naokiiwakami/analog2.0/02_panel/02_panel_doc_v1_0.pdf

## Analog 2.0 ドキュメンテーション

### Vol. 2

# パネルの製作

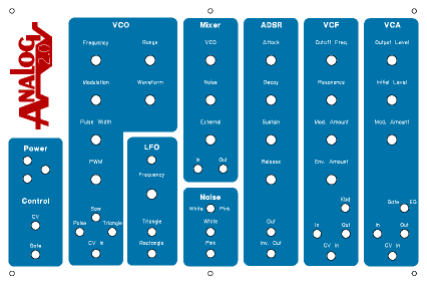
[picture p7: figure]

バージョン: 1.0
作成日：2008 年 1 月 25 日

Analog2.0 ドキュメンテーション
Vol.2 パネルの製作
Copyright (C) Naoki Iwakami. All rights reserved. | 2

目次

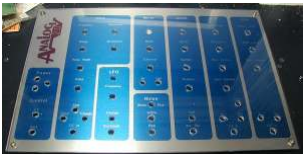
[picture p8: figure]

Copyright (C) Naoki Iwakami. All rights reserved. | 3
1. このドキュメントの目的

このドキュメントは、Analog2.0 のパネルの制作例を解説するものです。 Analog2.0 試作機におけるパネルの設計例をもとに、実際にパネルを製作する方法を解説 します。

パネルは、製作者の皆さんの工夫でどのように製作しても良く、このドキュメントで紹介 する制作方法は一例としてとらえてください。また、筐体の製作は Analog2.0 では紹介し ません。かわりに、試作機の実装例を写真で紹介します。最低限の手抜き製作の例です。

2. 製作例の紹介
2.1. パネル設計例の概要
ここで紹介するパネル設計例は、試作機で用いたものです。(図 2-1)

設計例では、図 2-2 のように、300mm x 200mm x 1mm のアルミ板と透明アクリル板で OHP シートを挟み込み構成します。OHP シートには、パネルのアートワークを印刷しま す。部品の取り付け穴は、重ねた状態でドリルを貫通させます。簡易的な設計ですが、以 下のメリットがあります

- パネル製作で一番面倒な塗装とレタリングを省くことができる
- ドリルで穴をあける際、OHP シートに目印をつけておけば、けがきをする必要がない

図 2-1 試作したパネル

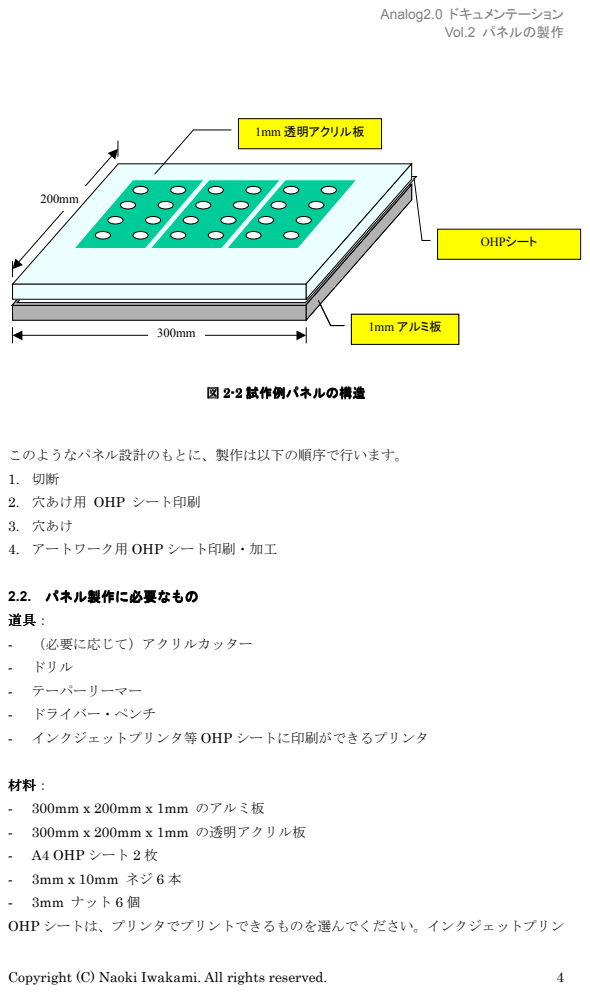
[picture p9: page 4]
Copyright (C) Naoki Iwakami. All rights reserved.; 図 2-2 試作例パネルの構造; 1mm アルミ板; OHPシート; 1mm 透明アクリル板

このようなパネル設計のもとに、製作は以下の順序で行います。
2. 穴あけ用 OHP シート印刷
3. 穴あけ
4. アートワーク用 OHP シート印刷・加工

2.2. パネル製作に必要なもの
- （必要に応じて）アクリルカッター
- ドリル
- テーパーリーマー
- ドライバー・ペンチ
- インクジェットプリンタ等 OHP シートに印刷ができるプリンタ

- 300mm x 200mm x 1mm のアルミ板
- 300mm x 200mm x 1mm の透明アクリル板
- A4 OHP シート 2 枚
- 3mm ナット 6 個
OHP シートは、プリンタでプリントできるものを選んでください。インクジェットプリン

Copyright (C) Naoki Iwakami. All rights reserved. | 5

タ・レーザープリンタ等、各プリンタタイプ用の OHP シートが販売されています。

ネジとナットは、重ね合わせたアルミ板・アクリル板・OHP シートを固定するために使い ます。

2.3. 材料の切断
パネルの製作にあたって、まずは始めに、材料のアルミ板とアクリルを希望の大きさに切 断します。最も推奨する方法は、初めから希望の大きさに切られている板を入手してしま うことです。道具を用意する必要がないし簡単で確実です。希望の大きさのものがない場 合にはホームセンターに依頼して切ってもらうと いう方法もあります。この試作機では アルミ板は 300mm x 200mm x 1mm のできあいのものを使い、アクリル板は自前で切断 しました。アクリル板の切断にはアクリルカッターを使います。

アルミ版を切断するには、金鋸を使う方法がすぐに思いつきますが、厚さ 1mm 程度のアル ミ板ならカッターナイフで切断できるようです。リンクが生きている限り以下のサイトが 参考になります。
http://webryalbum.biglobe.ne.jp/myalbum/1003289007923048b35a00dd242ffab118c63f430/65490414752138311

なお、A4 OHP シートのサイズは、297mm x 210mm で、300x200 と多少違っています。 はみ出る部分を切断する必要があります。これは仕上げ段階で行うと作業がしやすいです。

2.4. 穴あけ用 OHP シート印刷
次にパネルの穴あけを行います。試作例では、製作を簡単にするため、以下の手順で穴あ けを行います。

### 1. 穴あけ位置がマークしてあるアートワークを OHP シートに印刷する

### 2. 印刷した OHP シートを、アルミ板とアクリル板の間に挟みこむ

### 3. アートワークのマークに従い穴あけを行う

この節では、穴あけ用の OHP シートを印刷します。このドキュメントと同封してある panel_with_reference.pdf を印刷してください。以下は印刷時の注意事項です。

- プリント時の用紙選択にて、OHP シートを選びます。
- 高画質を選んでください。（色が濃いほうが作業しやすいため）
- 縮尺は 100%で印刷してください。

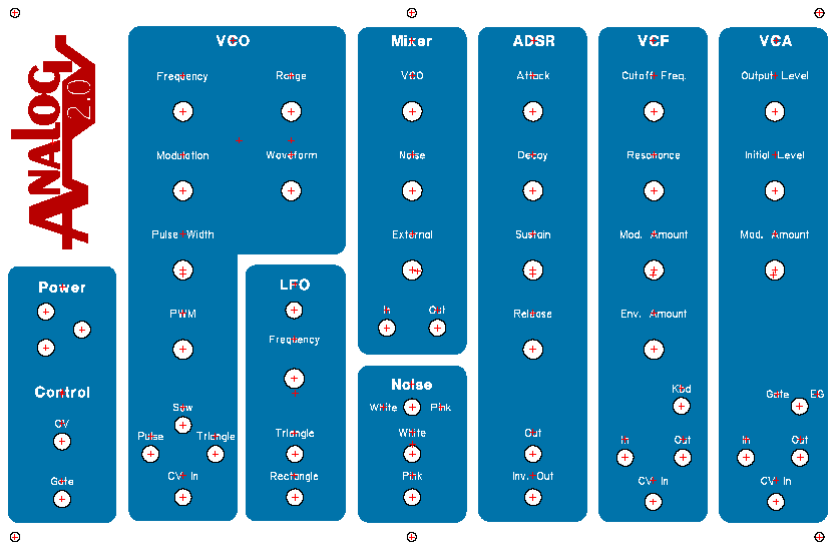
[picture p10: figure]

Copyright (C) Naoki Iwakami. All rights reserved. | 6
- 印刷後、すぐに印刷面に触らないようにしてください。OHP シートへの印刷は、イン クが乾きにくいことがよくあります。
- 印刷後、正しい縮尺で印刷されたかどうかの確認を必ず行ってください。方法はあとで 詳しく解説します。

参考までに、Adobe Reader 8 から印刷する際の、オプション設定は以下のとおりです。下 線が引いてあるところは、デフォルトから変更する必要のあるところです。

印刷範囲 | すべて
ページ部数 | 1
ページの拡大/縮小 | なし
自動回転と中央配置 | あり
ページサイズに合わせて用紙を選択 | なし

印刷を実行すると、図 2-3 のようなレイアウトが印刷されます。このレイアウトには、ドリ ル位置にセンターマーク（赤いプラス印）が打ってあるので、最終的なパネルシートとし ては使えません。ですが、パネルに挟み込むことで穴あけの際の位置決めに使います。こ のようにするとパネルへのけがきが不要になり、穴あけ作業が簡単になります。

図 2-3 ドリルガイド用 ドリルガイド用 OHP シート

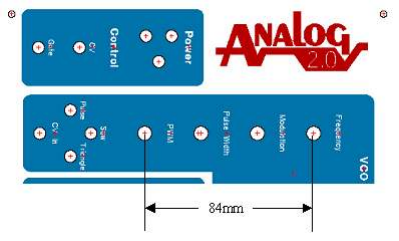
[picture p11: figure]

Copyright (C) Naoki Iwakami. All rights reserved. | 7

さて、OHP シートがプリントされたら、正しい縮尺で印刷されたかどうかチェックします。 印刷されたシートの、VCO 枠内 Frequency と PWM それぞれのセンターマークの距離 を測ります。84mm になっていれば OK です（図 2-4）。違っていたら、どこかに設定違い がないか確認してプリントしなおしてください。

図 2-4 OHP シート OHP シート縮尺確認

2.5. 穴あけ
OHP シートを印刷したら、いよいよ穴あけの開始です。 穴あけは、次のような手順で行います。

### 1. OHP シートをアルミ板とアクリル板で挟み込む

### 2. 四隅のネジ穴に穴をあけ、ネジで固定する

### 3. パネル部品用の穴をあける

OHP シートの固定
穴あけの最初の作業は、OHP シートをアルミ板とアクリル板で挟み込むことです。シート を正しい位置に配置して、しっかりと挟み込みます。位置あわせは、四隅のネジ穴位置が、 各々の角から等距離になるように行うとやりやすいと思います。ここで決まる配置が仕上 がりの配置になりますから注意深く作業してください。
アクリル板の防護シートは透明なら貼ったままにしておいてください。アルミ板の防護シ ートもまだ貼ったままにしておいてください。

OHP シートを固定する際、シートの両面の何箇所かに両面テープを貼っておくと作業が進 めやすいかもしれません。決めた位置からのずれを防止できるからです。

Copyright (C) Naoki Iwakami. All rights reserved. | 8

ネジ穴のドリル
OHP シートを固定したら穴あけ作業に入ります。まずは、隅のネジ穴からあけてゆきます。 ネジ穴は 3.2mm のドリルであけてください。
先にネジ穴をあけて、アクリル板・OHP シート・アルミ板を固定してしまうと、その後 はお互いがずれなくなるため、その後の作業が行いやすくなります。逆に、この作業で３ 枚がずれてしまうと、挽回するのは大変ですから、慎重に作業してください。

ネジ穴作業は、以下のような流れで行います。

### 1. まず、四隅のうちどれか一つに穴あけする。

### 2. あけた穴にネジを通してナットで締め固定してしまう。

### 3. 今あけた穴の対角に穴あけをし、ネジで固定する。

### 4. 残り二つの角の穴をあけ、ネジで固定する。

### 5. パネル上側と下側に残る二つのネジ穴をあける。ネジでの固定は必須ではない。

一つ一つのネジ穴は、以下の手順であけます。

### 1. アルミ版、OHP シート、アクリル板は重ねたまま穴あけする。

### 2. あける穴のセンターマーク位置にポンチで印をつける。なるべく垂直に見て印をつける

ようにしてポンチがセンターマークからずれないように気をつける。
3. 3.2mm ドリルを使って穴あけする。

パネル穴のドリル
ネジ穴をあけて、四隅をネジで固定したら、いよいよパネル部品の穴をあけてゆきます。 あけるべき穴のミリ数は、添付のシート panel_with_drill_sizes.pdf に記入してあります。 今度はドリル径が大きいので、位置ずれを起こさないように注意して作業してください。 下記は筆者がとったドリル方法です。比較的安い道具で失敗の少ない穴あけができます。

### 1. あける穴のセンターマークにあわせてポンチを打つ

2. 1.5mm 程度のドリルを使い、まずは小さな穴をあける。この作業はハンドドリルを使 ったほうがずれを起こしにくい。このドリルは細いほど良い。
3. 5mm 程度のドリルを使い、大きな穴をあける。

### 4. テーパーリーマーを使って穴を必要な大きさまで広げる。

ここまでできたら穴あけ作業は完了です。

Copyright (C) Naoki Iwakami. All rights reserved. | 9
2.6. アートワーク用 OHP シートの印刷・加工 穴あけが完了したら、仕上げの作業に入ります。
ここまで穴あけガイドに使っていた OHP シートは、作業を通して損傷しています。この シートは破棄して、アートワーク用に別の OHP シートを印刷して仕上げにはそちらを使 います。

アートワーク用の pdf ファイル panel.pdf を印刷してください。印刷の要領はドリル用の ものと同じです。縮尺の確認方法も同じですが、今回はセンタードリルがないので、ドリ ル穴のふちなどを使ってドリル穴間隔の計測をしてください。

次に、ネジで固定してあるアクリル板、アルミ板をいったんはずして、新しい OHP シー トを挟み込みます。その際、ドリル穴部分のシートが邪魔になるので、以下の方法いずれ かで取り除きます。

### 1. 革製品用のポンチを使って穴を打ち抜く

### 2. OHP シートをアクリルとアルミで挟みこんでネジで固定した後、ドリル穴部分のシー

トをカッターナイフでくりぬく

筆者は 1 の方法を使いました。きれいに打ち抜くには若干練習が必要ですが、慣れると能 率よく作業できます。

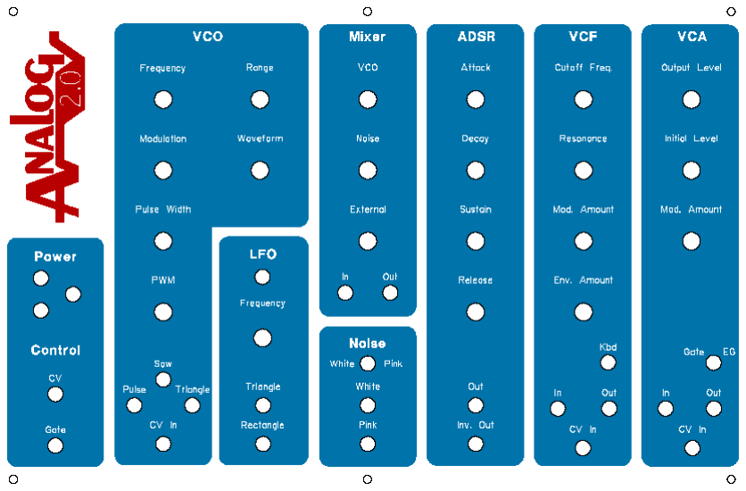
[picture p12: figure]

Copyright (C) Naoki Iwakami. All rights reserved. | 10

図 2-5 アートワーク用 OHP シートのレイアウト

さて、これでパネルは出来上がりました。大体図 2-1 のようになりましたか？

3. 筐体について

Analog2.0 で紹介するパネルの製作例は以上です。しかし、このままではシンセサイザー モジュールの製作はままならないはずです。パネルを立ててもすぐ倒れてしまうからです。

製作を進めるには、パネルを何かのケースに固定する必要があります。もっとも良いのは 筐体に収めてしまうことです。筐体を設計する際には、内側の奥行きが最低でも 100mm 必 要です。できれば 120mm 程度はあったほうが安心です。

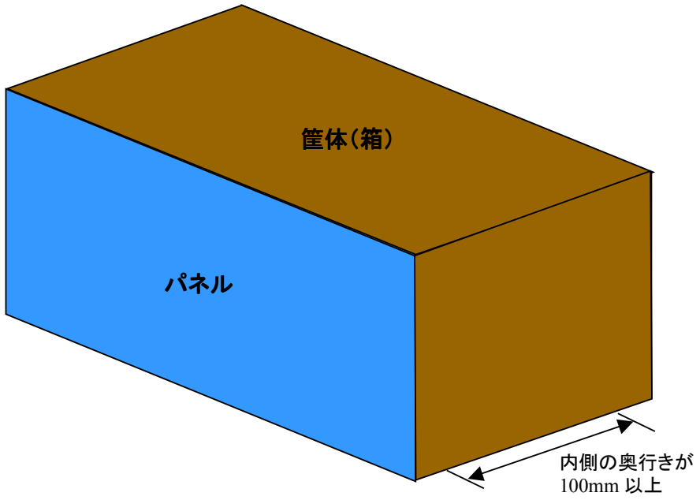
[picture p13: figure]
内側の奥行きが; パネル
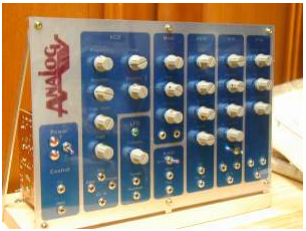
[picture p14: figure]

Copyright (C) Naoki Iwakami. All rights reserved. | 11

図 2-6 筐体のイメージ

試作機では、筐体製作の手間を省いて、木板に L 字金具で固定するだけとしました。決 して推奨するものではありませんが、このあたりが最低ラインという目安にでもなれば幸 いです。
ちなみに、試作例では、パネルのたわみを軽減するため、上側を L アングルで補強してあ ります。

図 2-7 Analog2.0 Analog2.0 試作機の概観

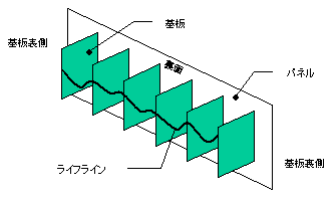
[picture p15: figure]

Copyright (C) Naoki Iwakami. All rights reserved. | 12

付録 A: パネルの独自設計について

パネルを独自に設計して製作することは、Analog2.0 の目的と合致しており、大いに行って いただきたいことです。カスタマイズの足がかりとするため、設計のもとファイルを添付 しました (analog20.FPD)。このファイルを閲覧・編集するには、Front Panel Designer (http://www.frontpanelexpress.com/index.php?id=11) というソフトウェアが必要です。

Analog2.0 では、図 3-1 のイメージのように、基板がパネルに直接取り付けられるように 設計されています。この取り付け方針を維持するためには、パネルを独自設計するにあた って、いくつかの点に注意してください。

なお、基板のパネルマウントにこだわらない場合には、下記の制約事項はあてはまりませ ん。この場合基板とパネル上の部品はリード線で接続することになります。実装が面倒に なるかわりにパネル設計の自由度は増します。

ボリュームの縦間隔を変更しない
ボリュームの縦の位置関係は、基板の設計によって制約を受けています。基板をパネルマ ウントできるようにしておくためには、ボリュームの縦の位置関係を維持する必要があり ます。ボリュームの位置関係が維持されていれば、回転・並行移動は問題ありません。

基板間の距離を保つ
図 3-1 のように、Analog2.0 は機能モジュールごとに基板を分けています。パネルマウン トを維持したままパネルレイアウトを変更する場合、基板同士が近づき過ぎないようにデ ザインを配慮する必要があります。

図 3-1 パネルへの基板マウントのイメージ
