naokiiwakami/analog2.0/07_eg/eg_doc.pdf

## Analog 2.0 ドキュメンテーション

### Vol. 7

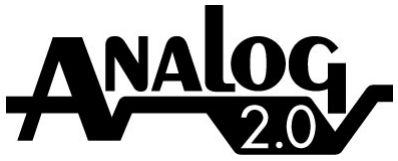
[picture p63: figure]

# エンベロープ・ジェネレータ ・ジェネレータの製作

バージョン：2.1
作成日：2009 年 12 月 14 日

Analog2.0 ドキュメンテーション
Vol.7 エンベロープ・ジェネレータの製作
Copyright (C) 2009 Naoki Iwakami. All rights reserved. | 2

目次

1. このドキュメントについて | 3 ...... 3
2. エンベロープ・ジェネレータモジュール ・ジェネレータモジュールの製作 | 4 ...... 4

Copyright (C) 2009 Naoki Iwakami. All rights reserved. | 3
1. このドキュメントについて

このドキュメントは、アナログシンセサイザーシステム Analog2.0 のエンベロープ・ジェ ネレータモジュールの製作方法を解説します。

このドキュメントは、利用者がすでに以下のドキュメントを参考に製作を進めていること を前提に書かれています。
- Analog2.0 スターターキット
- vol.4 ノイズジェネレータとミキサの製作
- vol.5 VCA の製作
- vol.6 VCO の制作

更新履歴

バージョン | 日付 | 変更内容
2.0 | 2009/11/19 | Analog2.0 ドキュメントバージョン 2.0 - 回路設計を見直し。 - それにあわせてドキュメントを改訂。
2.1 | 2009/12/14 | -図 2-7 配線図の間違いを修正。 Inv 出力と Non-Inv 出力が逆転。

Copyright (C) 2009 Naoki Iwakami. All rights reserved. | 4
2. エンベロープ・ジェネレータモジュール ・ジェネレータモジュールの製作
2.1. 製作の流れ
モジュール製作の流れは、毎度同じ以下の手順です。
- 部品の入手
- 基板の製作
- 基板へ部品を取り付ける
- パネル部品の取り付け
- 基板の配線確認
- 動作確認
2.2. 製作するモジュールの概要
2.2.1. 機能
この記事では、エンベロープ・ジェネレータ(EG)モジュールを製作します。
EG は、図 2-1 のように、ゲート信号を入力にして、ADSR と呼ばれるエンベロープ情報を 出力します。

図 2-1 エンベロープ・ジェネレータ ・ジェネレータの概念図

図 2-2 は、EG の入力と出力の関係を説明する図です。まず、ゲート入力のない初期状態で は、出力もゼロです。ゲート信号が立ち上がると、EG の動作が開始します。最初に、出力 は、ゼロから最大値まで立ち上がります。この立ち上がり時間は Attack Time (A) で設定 します。出力が最大値に達すると、減衰を開始します。この速さは Decay Time (D) で設 定します。ゲート入力がある間は、減衰後 Sustain Level (S) で設定したレベルに落ち着き ます。そして、ゲートをオフにすると、ゼロに向けて減衰します。この速さは、Release Time
(R) で設定します。EG は、このように、時間的に変動する CV パタンを発生し、シンセサ イザーの音に変化を与えます。
ゲート信号 | Envelope
| Generator

ADSR出力

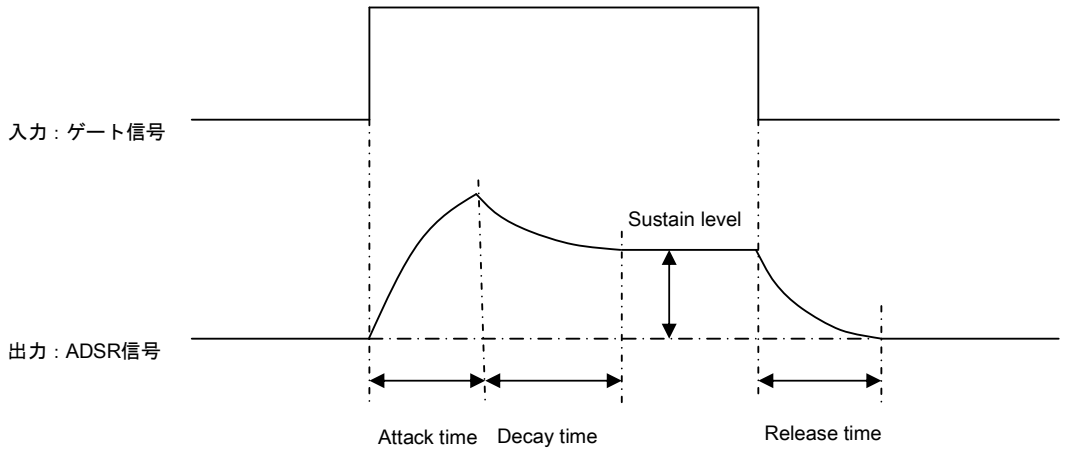
[picture p64: figure]
Attack time Decay time; Sustain level; Release time; 入力：ゲート信号; 出力：ADSR信号
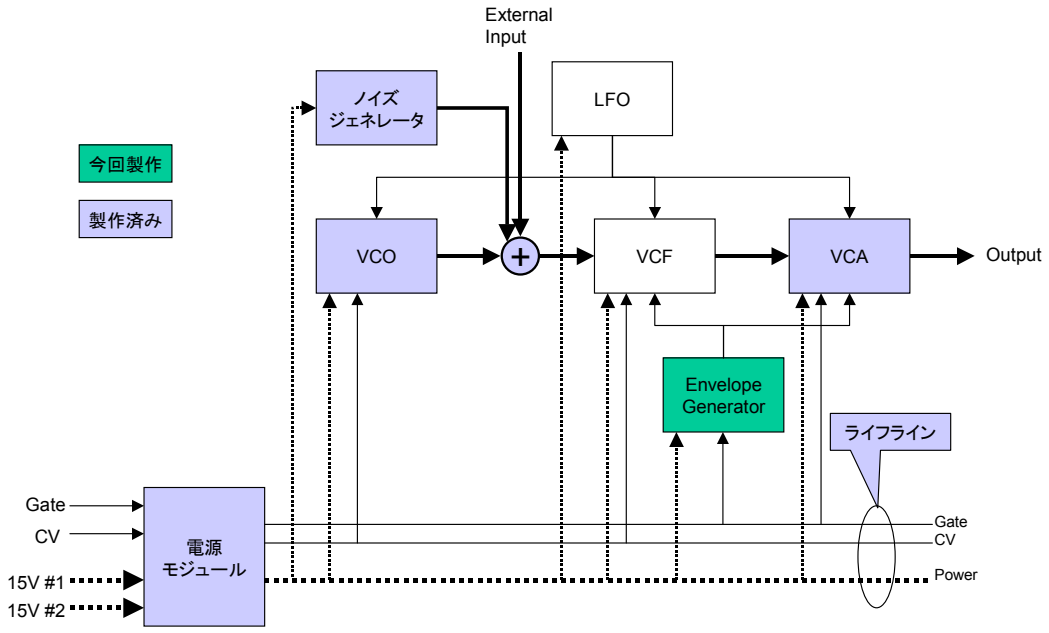
[picture p65: figure]
VCO; ノイズ ジェネレータ; VCF; VCA; LFO; Envelope Generator; External Input; Output; Gate; 電源 モジュール 15V #1; ライフライン; Gate CV; Power; 今回製作; 製作済み

Copyright (C) 2009 Naoki Iwakami. All rights reserved. | 5

図 2-2 エンベロープ・ジェネレータの入力と出力

2.2.2. システム内での位置づけ

図 2-3 に、Analog2.0 製作システムの構成の中での EG の位置づけを示します。EG は、 Analog2.0 のメインの制御モジュールで、VCF、VCA といった音加工モジュールの動作に 変化を与えます。

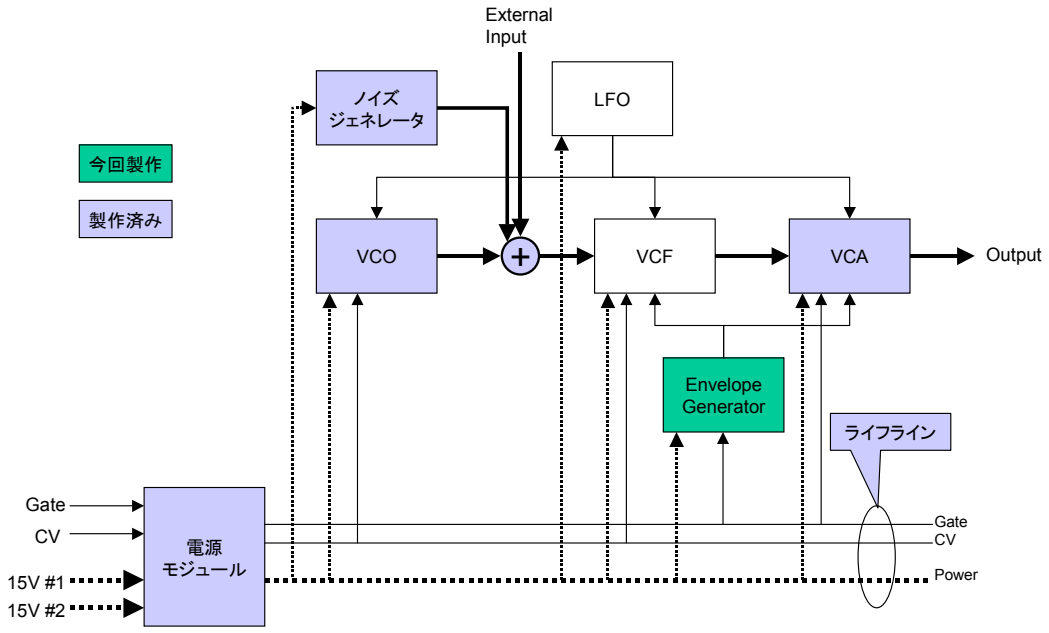
[picture p66: figure]
VCO; ノイズ ジェネレータ; VCF; VCA; LFO; Envelope Generator; External Input; Output; Gate; 電源 モジュール 15V #1; ライフライン; Gate CV; Power; 今回製作; 製作済み
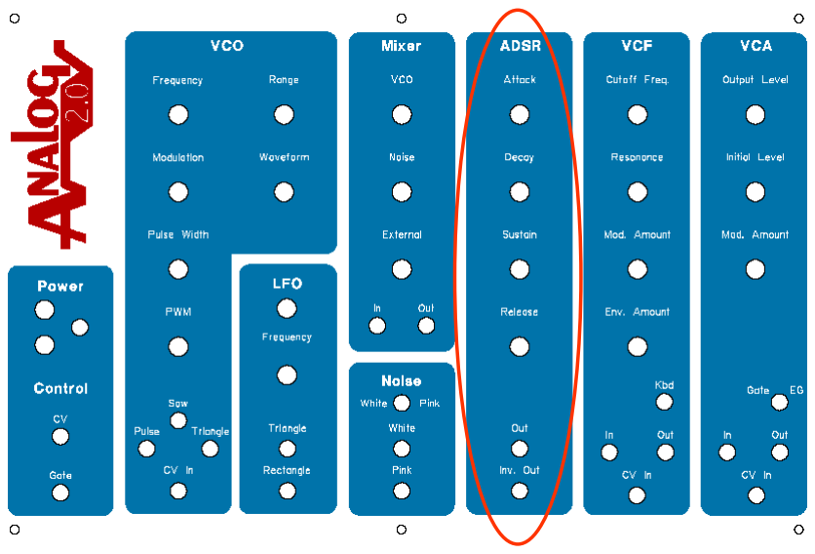
[picture p67: figure]

Copyright (C) 2009 Naoki Iwakami. All rights reserved. | 6

図 2-3 EG の位置づけ

パネルの中では、EG は図 2-4 のように位置づけられています。

Copyright (C) 2009 Naoki Iwakami. All rights reserved. | 7

図 2-4 パネル中での位置づけ

2.2.3. 仕様
EG の仕様は以下のとおりです。
- 入力ゲートレベル : off 0V on 5V
- 出力信号レベル : 0 to 8V (非反転出力) 0 to –8V (反転出力)
- パラメータ : Attack Time / Decay Time / Sustain Level / Release Time

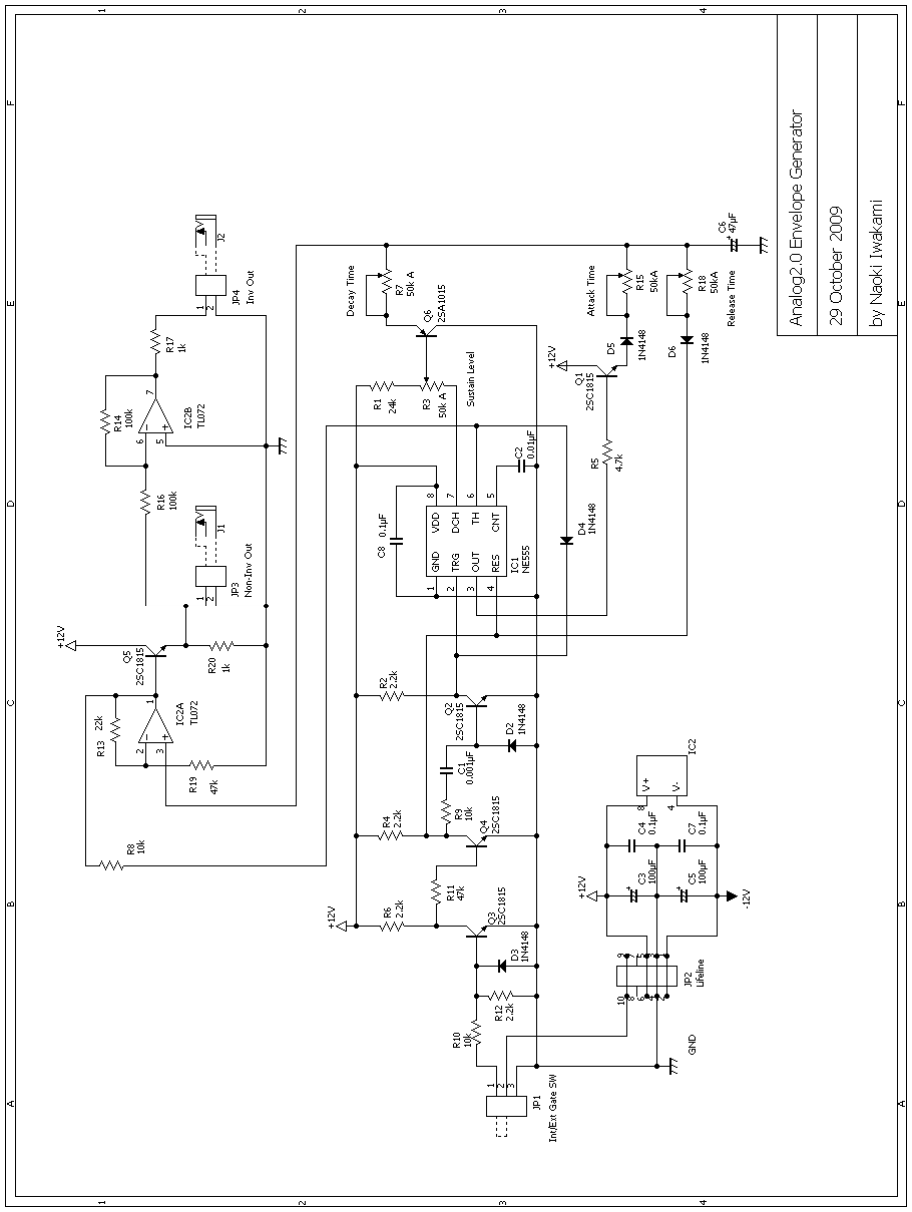
[picture p68: figure]

Copyright (C) 2009 Naoki Iwakami. All rights reserved. | 8
2.2.4. 回路
製作する EG の回路図は図 2-5 のとおりです。

図 2-5 EG モジュールの回路図

Copyright (C) 2009 Naoki Iwakami. All rights reserved. | 9
2.3. 部品の入手
それでは、いよいよ製作に入ります。製作に必要なパーツは以下のとおりです。製作にあ たっては、まずこれらのパーツを入手してください。

注意：ダイオードの番号は D1 が抜けていて、D2 から始まります。D6 までありますが必 要なのは 5 本です。

表 2-1: EG の製作に必要な部品(基板内)

部品 番号 | デバイス名 | 値/型番 | 備考
C1 | 積層セラミックコンデンサ | 0.001μF | セラミックコンデンサでも可
C2 | 積層セラミックコンデンサ | 0.01μF | セラミックコンデンサでも可
C3 | 電解コンデンサ | 100μF
C4 | 積層セラミックコンデンサ | 0.1μF | セラミックコンデンサでも可
C5 | 電解コンデンサ | 100μF
C6 | 電解コンデンサ | 47μF
C7 | 積層セラミックコンデンサ | 0.1μF | セラミックコンデンサでも可
C8 | 積層セラミックコンデンサ | 0.1μF | セラミックコンデンサでも可
D2 | ダイオード | 1N4148
D3 | ダイオード | 1N4148
D4 | ダイオード | 1N4148
D5 | ダイオード | 1N4148
D6 | ダイオード | 1N4148
IC1 | タイマ IC | NE555
IC2 | オペアンプ | TL072
JP1 | ピンヘッダ 2.5mm ピッチ | 1x3 | Int/Ext Gate SW
JP2 | ピンヘッダ 2.5mm ピッチ | 2x5 | Lifeline
JP3 | ピンヘッダ 2.5mm ピッチ | 1x2 | Non-Inv Out
JP4 | ピンヘッダ 2.5mm ピッチ | 1x2 | Inv Out
Q1 | トランジスタ | 2SC1815
Q2 | トランジスタ | 2SC1815
Q3 | トランジスタ | 2SC1815
Q4 | トランジスタ | 2SC1815
Q5 | トランジスタ | 2SC1815

Copyright (C) 2009 Naoki Iwakami. All rights reserved. | 10
Q6 | トランジスタ | 2SA1015
R1 | カーボン抵抗 | 24kΩ | 1/4W 5%
R2 | カーボン抵抗 | 2.2kΩ | 1/4W 5%
R3 | 可変抵抗 | 50kΩ A
R4 | カーボン抵抗 | 2.2kΩ | 1/4W 5%
R5 | カーボン抵抗 | 4.7kΩ | 1/4W 5%
R6 | カーボン抵抗 | 2.2kΩ | 1/4W 5%
R7 | 可変抵抗 | 50kΩ A
R8 | カーボン抵抗 | 10kΩ | 1/4W 5%
R9 | カーボン抵抗 | 10kΩ | 1/4W 5%
R10 | カーボン抵抗 | 10kΩ | 1/4W 5%
R11 | カーボン抵抗 | 47kΩ | 1/4W 5%
R12 | カーボン抵抗 | 2.2kΩ | 1/4W 5%
R13 | カーボン抵抗 | 22kΩ | 1/4W 5%
R14 | カーボン抵抗 | 100kΩ | 1/4W 5%
R15 | 可変抵抗 | 50kΩ A
R16 | カーボン抵抗 | 100kΩ | 1/4W 5%
R17 | カーボン抵抗 | 1kΩ | 1/4W 5%
R18 | 可変抵抗 | 50kΩ A
R19 | カーボン抵抗 | 47kΩ | 1/4W 5%
R20 | カーボン抵抗 | 1kΩ | 1/4W 5%

表 2-2: EG の製作に必要な部品(基板外)

J1 | 3.5mm ピンジャック | Non-Inv Out
J2 | 3.5mm ピンジャック | Inv Out
2.4. 基板へ部品を取り付け

図 2-6 は、今回製作するプリント基板の配線図です。この基板には接続されていないパッド

が多数配置されています。これはユニバーサル基板です。回路を改造する場合に使ってく ださい。
注意１：この基板には 1 本ジャンパ線がありますが、シルクスクリーンに印刷されていま せん。図 2-6 を見て忘れずジャンパ線を取り付けてください。
注意２：R11 の隣（R6 の反対側）の抵抗は R1 です。D6 の文字と重なって見えないかもし

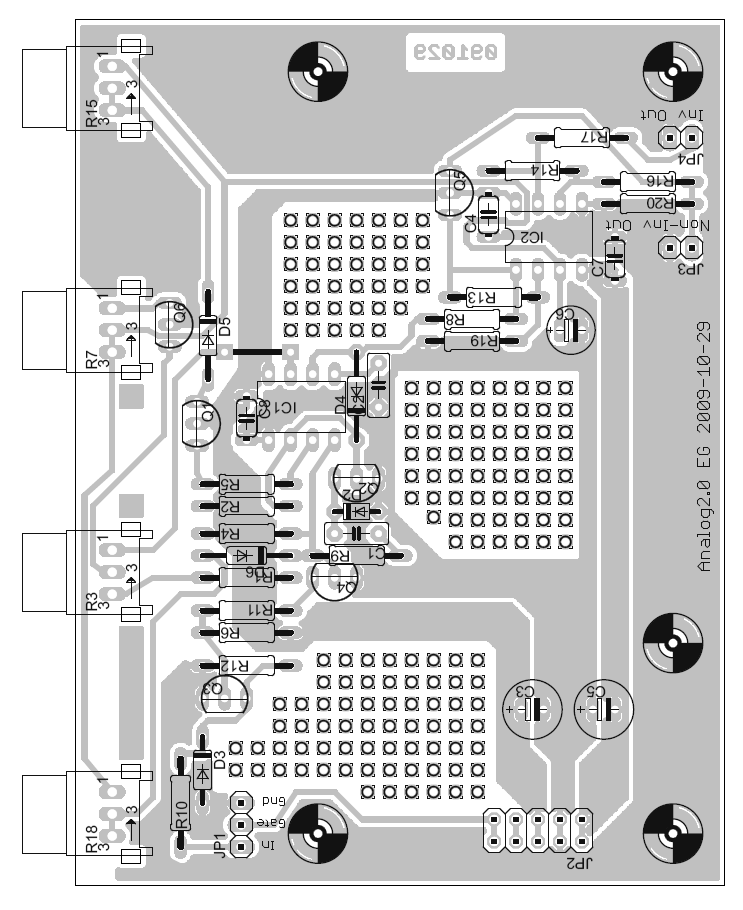
[picture p69: figure]

Copyright (C) 2009 Naoki Iwakami. All rights reserved. | 11

れません。

図 2-6 EG 基板の配線図

2.5. パネル部品の取り付け

基板部品を取り付けたら、パネルに取り付ける部品（基板外の部品）を配線します。

Copyright (C) 2009 Naoki Iwakami. All rights reserved. | 12

図 2-7 のように、ピンヘッダと、ミニジャックをリード線でつなぎます。非反転の出力は、 ジャックに出した後、延長して VCF モジュールと VCA モジュールそれぞれの EG In 端 子にも接続します。VCF モジュールはまだ完成していないので、コネクタだけ準備して未 接続の状態にしておいてください。
JP1 のジャンパは、PC の部品などで使われているものが流用できます。（図 2-8）

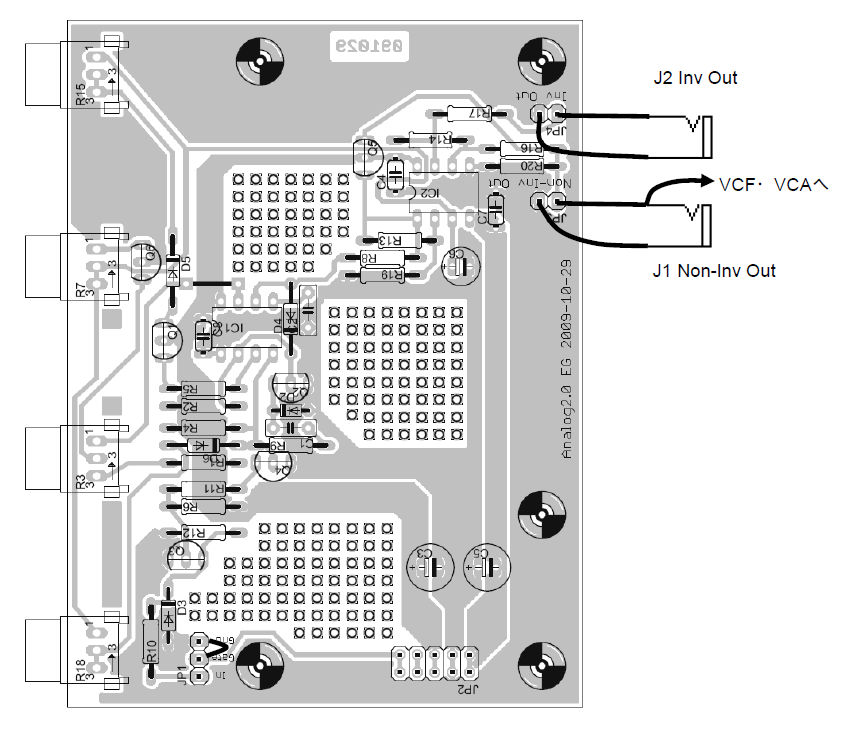
[picture p70: figure]

Copyright (C) 2009 Naoki Iwakami. All rights reserved. | 13

図 2-7 の実体配線図では、接続を見やすくするためにあえて大きくリード線を取り回してい ますが、実際の配線ではできるだけリード線がコンパクトになるように心がけてください。 図 2-9 の写真は、基板をパネルに実装したところの例です。図 2-10 は、パネルへの実装を 表側から見たところです。写真からもわかるように、基板はボリューム軸をナットで締め ることによって固定します。

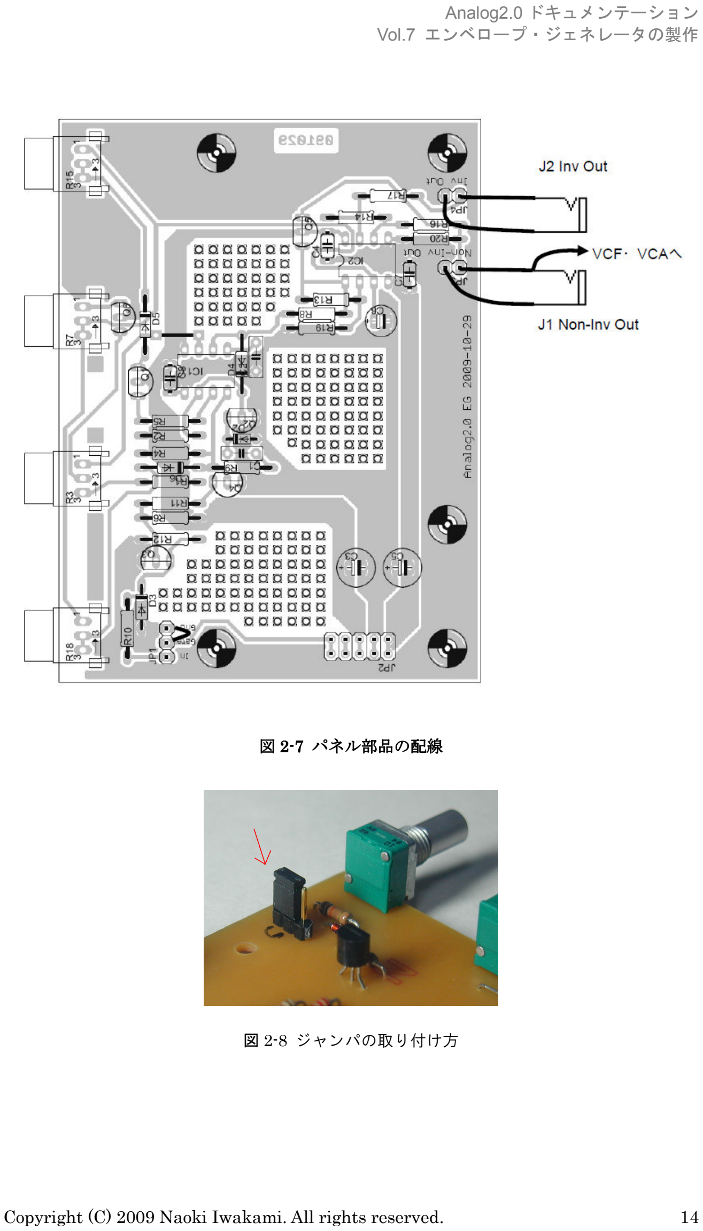
[picture p71: page 14]

Copyright (C) 2009 Naoki Iwakami. All rights reserved. | 14

図 2-7 パネル部品の配線

図 2-8 ジャンパの取り付け方

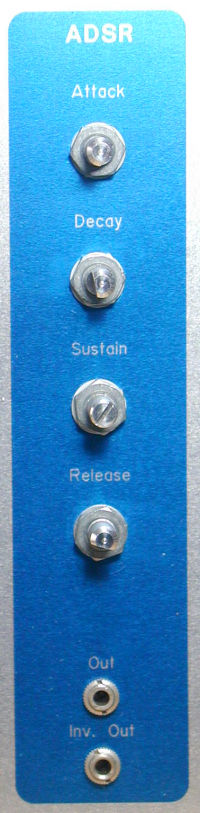
[picture p72: figure]
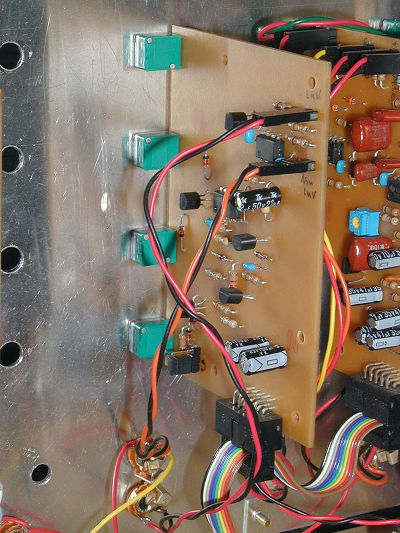
[picture p73: figure]

Copyright (C) 2009 Naoki Iwakami. All rights reserved. | 15
図 2-9 パネルへの実装例（裏側） | 図 2-10 パネルへの実装例（表側）
2.6. 基板の配線確認
ここまでで、EG モジュールの組み立ては完了です。いつものように、電源投入をする前に 必ず配線確認を行います。万一配線間違いがあると、正常に動作しないだけでなく、場合 によっては部品を破損してしまいます。以下のチェックリストを見ながら正しく配線され ているかどうか確認してください。

［ ］ 抵抗器は正しい場所に正しい値が取り付けられているか？
［ ］ コンデンサは正しい場所に正しい種類が正しい値で取り付けられているか？ ［ ］ 電解コンデンサは正しい向きに取り付けられているか？
［ ］ ダイオードは正しい場所に正しい向きで取り付けられているか？
［ ］ トランジスタは正しい場所に正しい向きで取り付けられているか？


Copyright (C) 2009 Naoki Iwakami. All rights reserved. | 16

［ ］ IC は正しい場所に正しい向きで取り付けられているか？
［ ］ ジャック・ピンヘッダは正しい場所に取り付けられているか？
［ ］ 基板を裏返して、ハンダ付け箇所をチェックする。隣り合った銅箔パタンが、ハン ダでショートしているハンダブリッジが発生していないか？
［ ］ ハンダ付けがイモハンダになっている箇所はないか？部品の本体をグラグラ揺らし てハンダ付け箇所のリードが動く場合、ほぼ確実にイモハンダです。イモハンダは 時間が経過すると、剥離してしまうので、見つけたらハンダ付けをやり直します。

図 2-11 正しいハンダとイモハンダ

2.7. 動作確認
では、いよいよ動作確認です。今回は調整箇所がないため、動作確認のみとなります。動 作確認には、以下を準備してください。
- MInI Board または、ゲート信号を発生する装置
- アナログテスター

今回は、テスターにアナログのものを使います。ディジタルテスターは適しません。アナ ログテスターを持たない場合には、VCA からの音をたよりに動作確認を行ってください。 VCA からの音を聴くには、ミキサの Noise ボリュームを大きくして、VCA 出力をアンプに つなぎます。

動作確認は、次の手順で行ってください。

### 1. MInI Board を Analog2.0 に接続する

### 2. 電源を投入する

### 3. つまみを次のように設定する→ A：最小、D：最小、S：最大、R：最小

### 4. EG の出力にテスターをあてる。テスターのレンジは、12V よりも大きくする。

Copyright (C) 2009 Naoki Iwakami. All rights reserved. | 17

### 5. MInI Board の任意のキーを押し、ゲートを発生させる。これに伴い、EG の出力が 8V

程度まで上がることを確認する。

### 6. S を中点に動かし、ゲートを再度発生する。EG の出力が 4V 程度まで上がることを確

認する。

### 7. A の値を上げてゆきながら、何度かゲートを発生させる。EG の立ち上がりが徐々に遅

くなってゆくことを確認する。立ち上がりで、EG の出力が最大に達すると、急速に 4V 程度まで落ち込む。

### 8. A の値を適当にセットし、D の値を上げてゆきながら、何度かゲートを発生させる。立

ち上がり後最大値から S の値に落ちてゆくスピードが少しずつ遅くなってゆくことを 確認する。

### 9. R の値を上げてゆきながら、何度かゲートを ON/OFF させる。ゲート OFF からの出

力の減衰が序所に遅くなってゆくことを確認する。

正常動作を確認したら、エンベロープ・ジェネレータの製作は完了です。これでいよいよ、 CV/Gate を入れて音作りや演奏ができるようになりました。
