naokiiwakami/analog2.0/02_panel/panel_with_drill_sizes.pdf

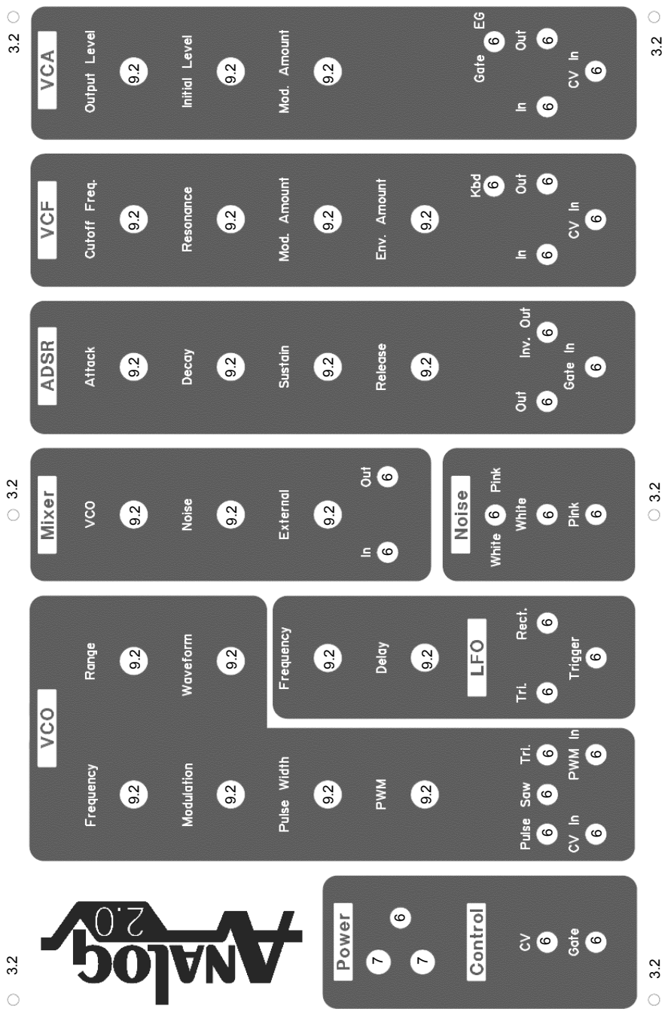
[picture p108: page 1]

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
3.2 3.2 3.2
3.2 3.2 3.2

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
