naokiiwakami/analog2.0/02_panel/panel.png

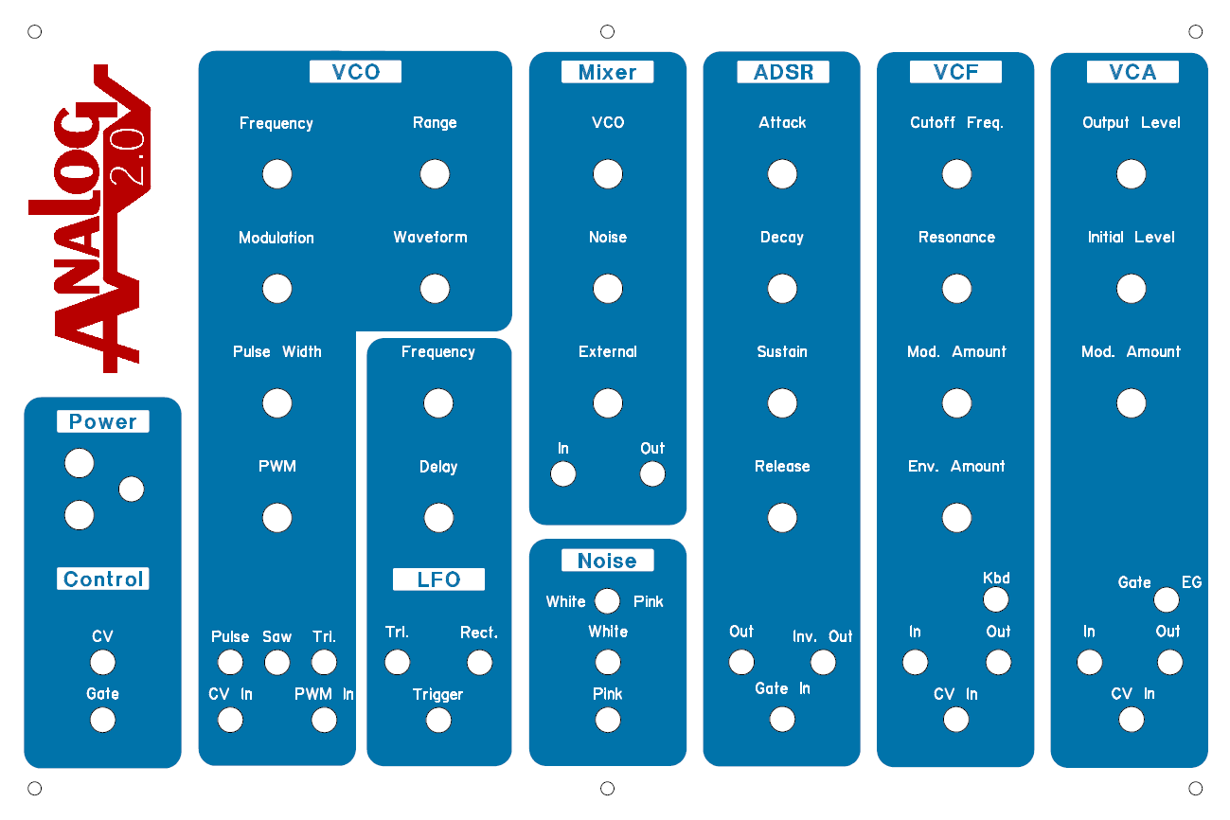
02_panel/panel.png
