naokiiwakami/analog2.0/04_noise_mixer/noise_mixer_sch.png

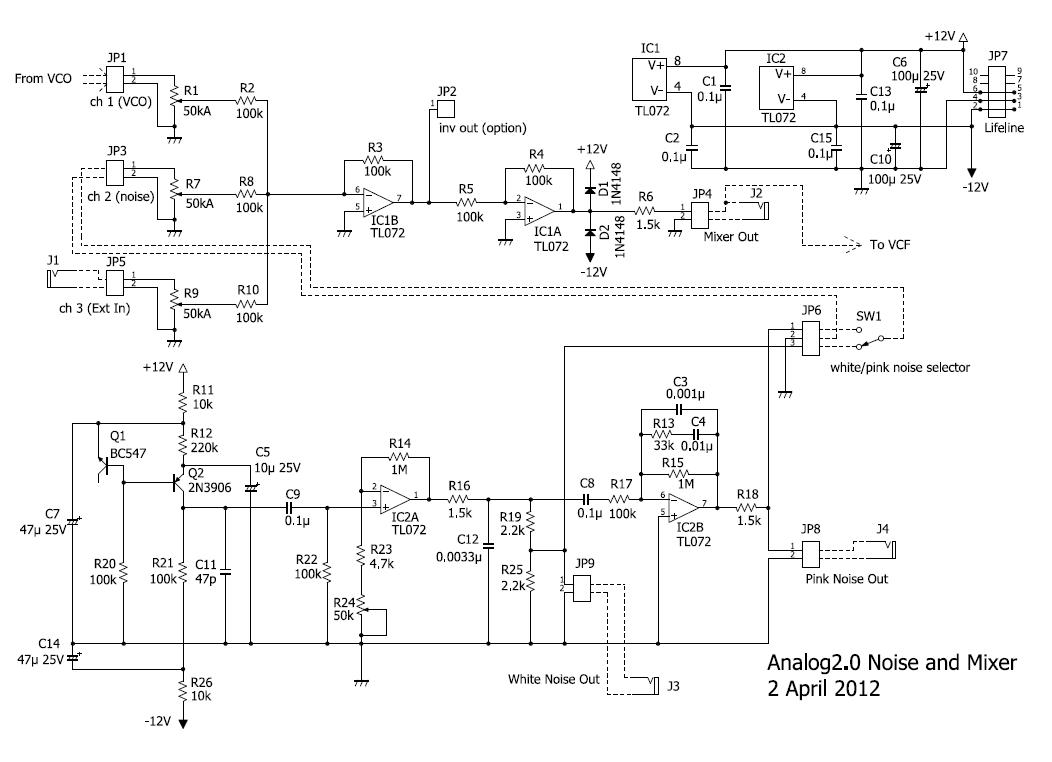
04_noise_mixer/noise_mixer_sch.png
