naokiiwakami/analog2.0/05_vca/vca_sch.png

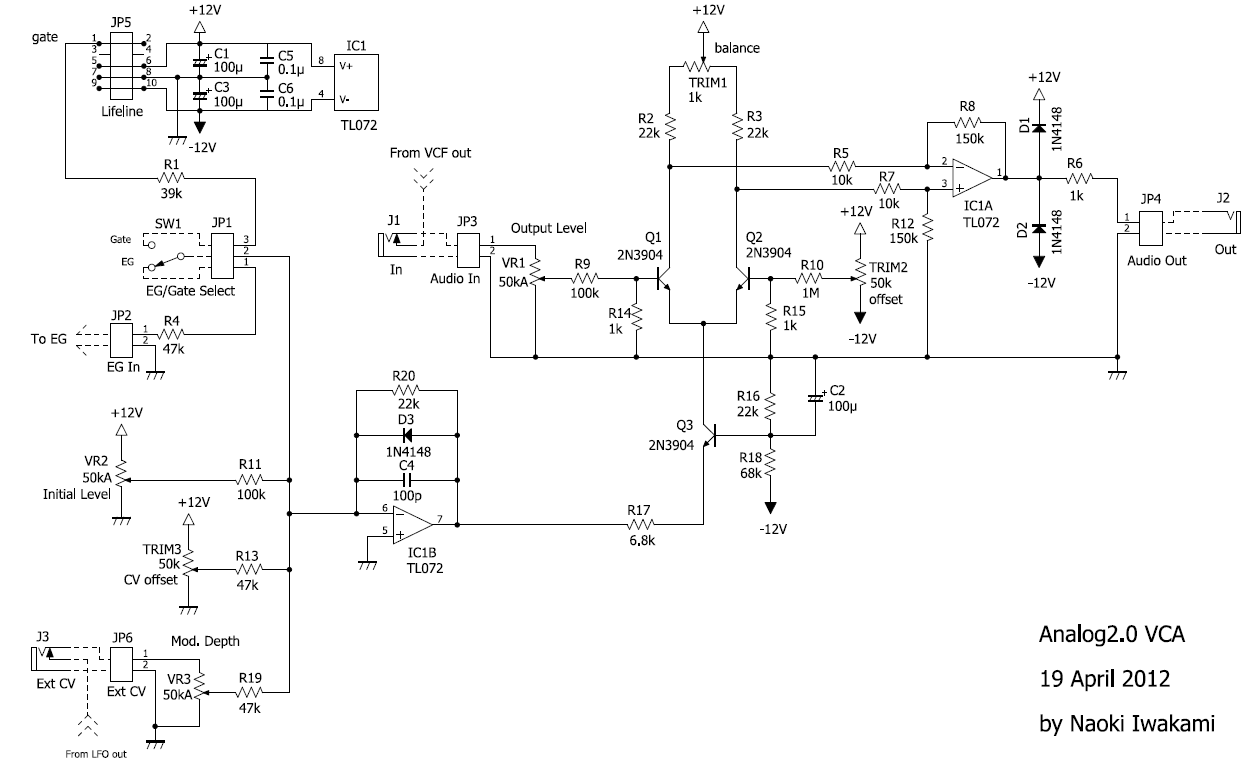
05_vca/vca_sch.png
