naokiiwakami/analog2.0/06_vco/vco_sch.png

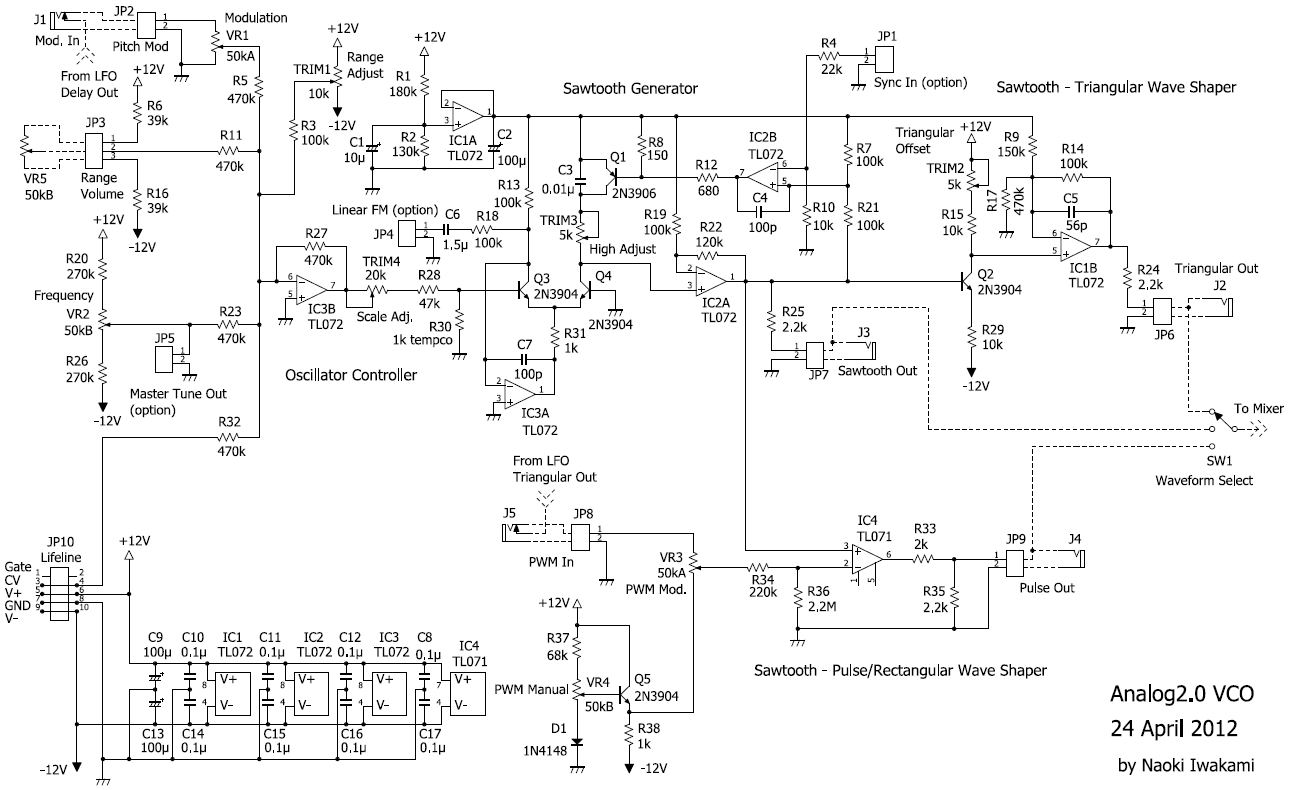
06_vco/vco_sch.png
