naokiiwakami/analog2.0/07_eg/eg_sch.png

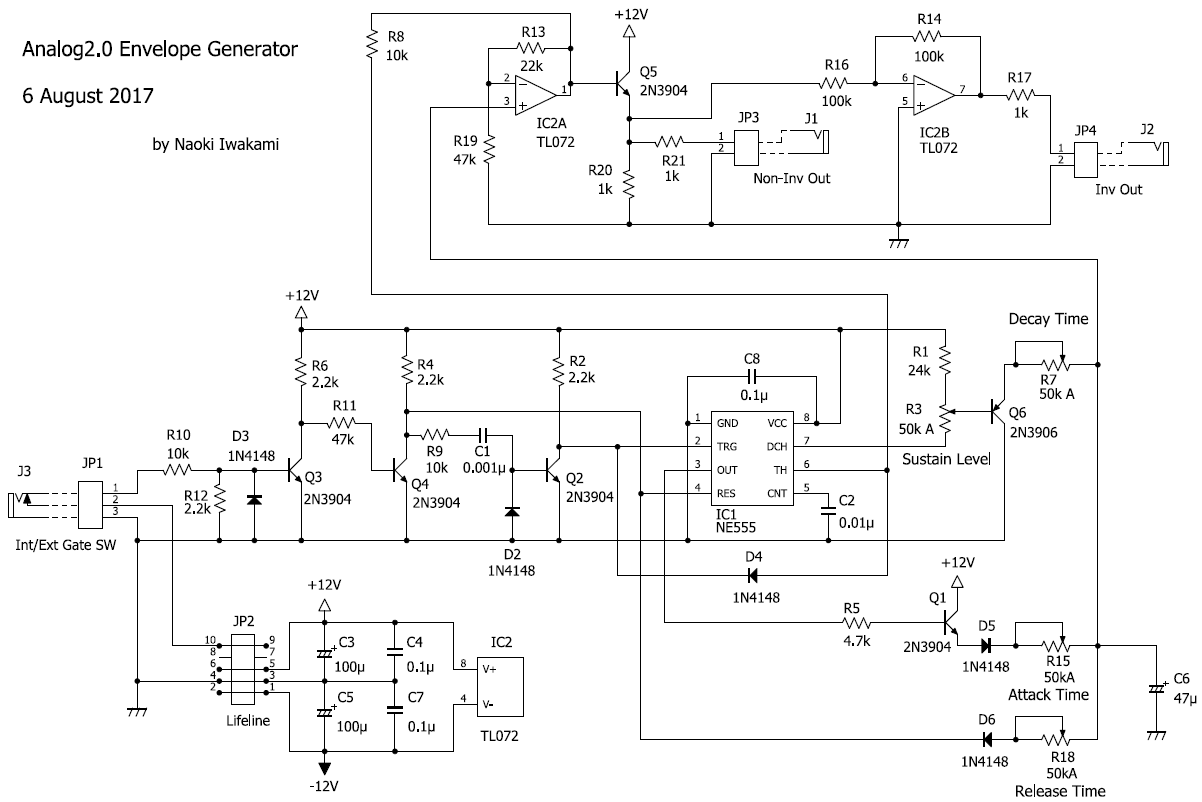
07_eg/eg_sch.png
