naokiiwakami/analog2.0/08_lfo/lfo_sch.png

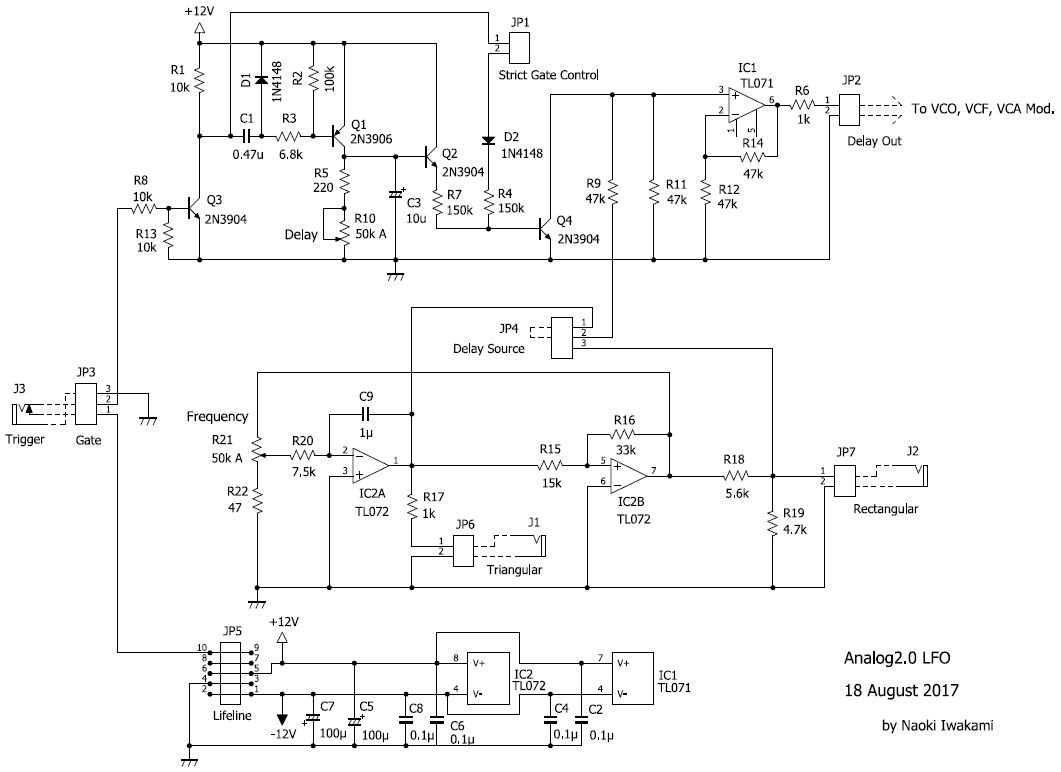
08_lfo/lfo_sch.png
