naokiiwakami/analog2.0/09_vcf/vcf_sch.png

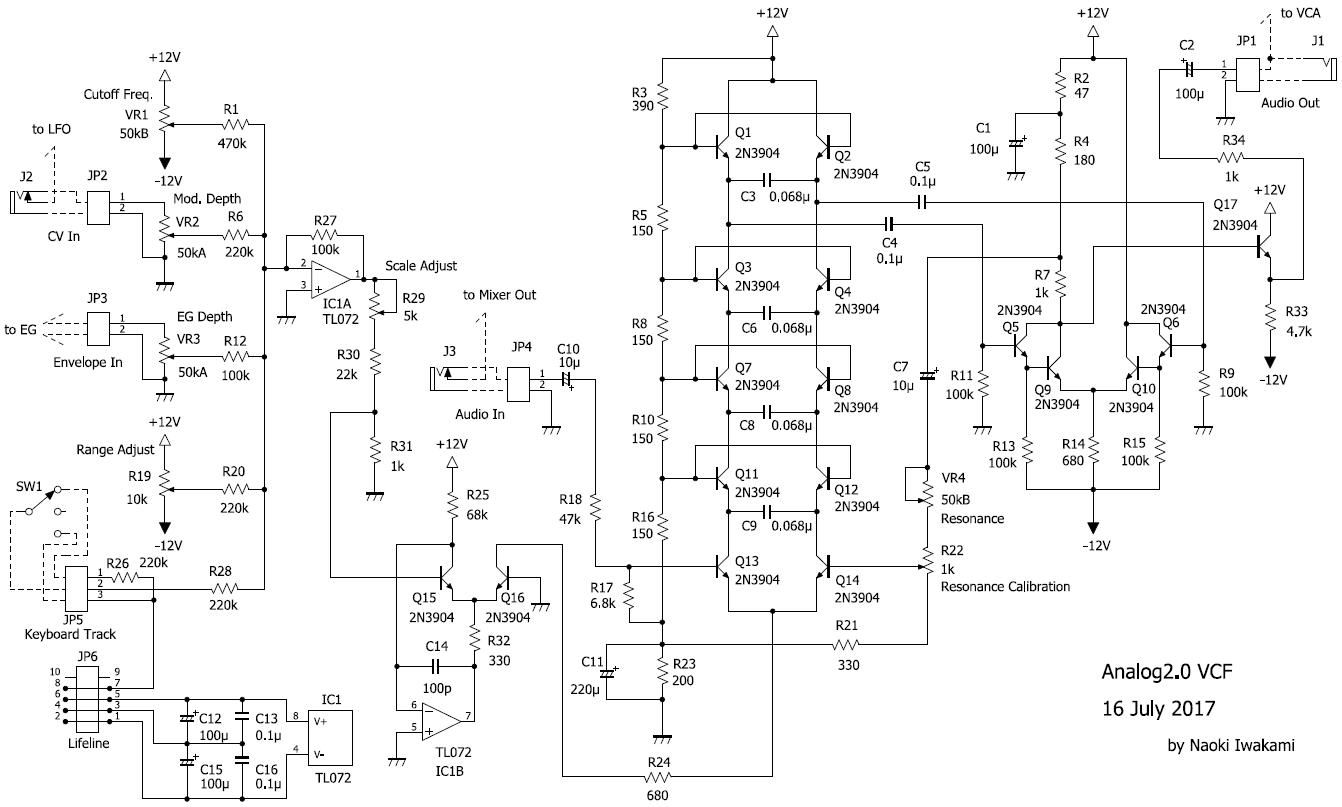
09_vcf/vcf_sch.png
