naokiiwakami/analog2.0/doc/analog20.jpg

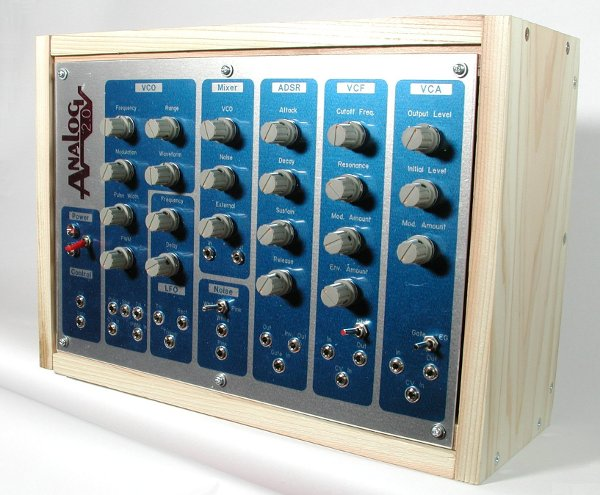
doc/analog20.jpg
