naokiiwakami/analog2.0/01_overview/wiring1.jpg

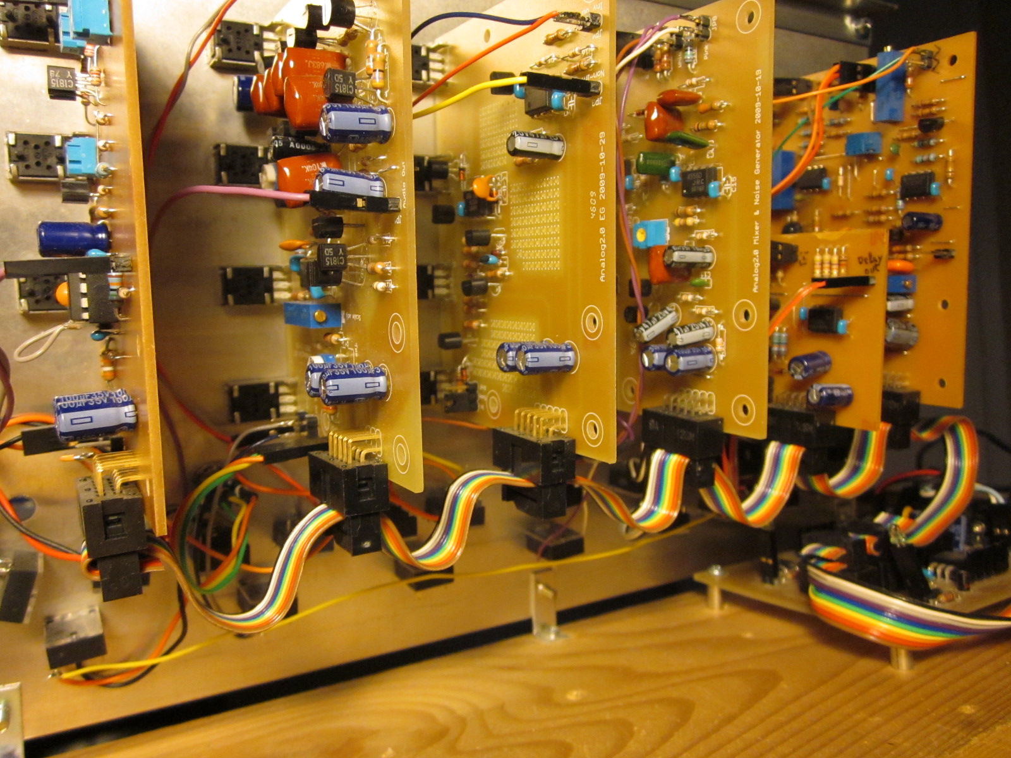
01_overview/wiring1.jpg
