naokiiwakami/analog2.0/08_lfo/lfo_brd.pdf

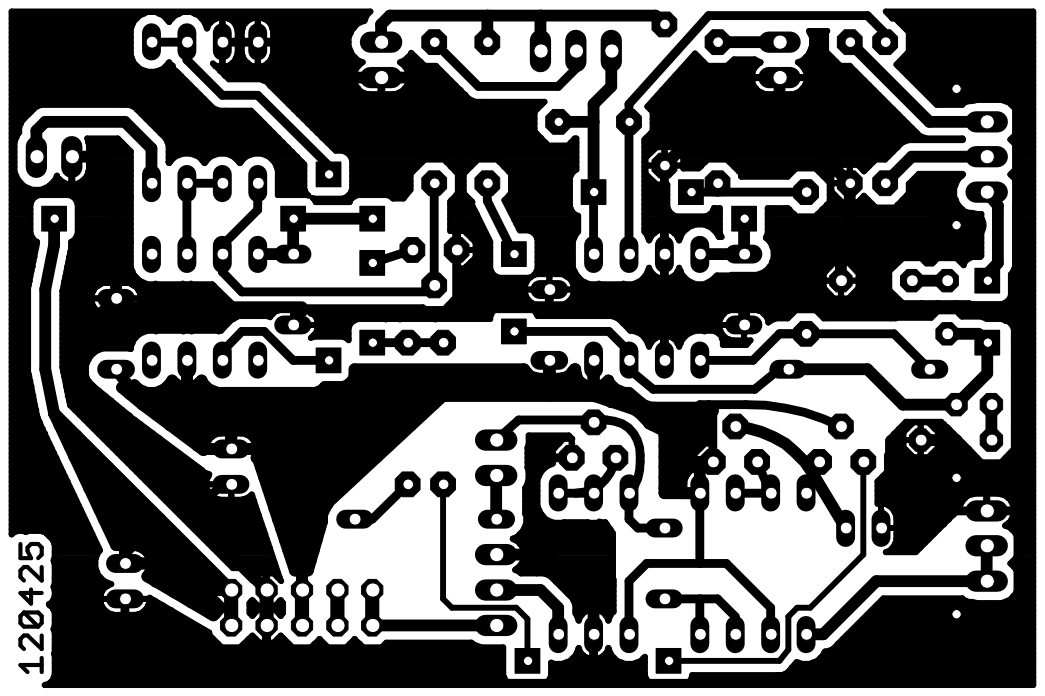
[picture p151: page 1]
