naokiiwakami/analog2.0/08_lfo/lfo_brd_cmp.pdf

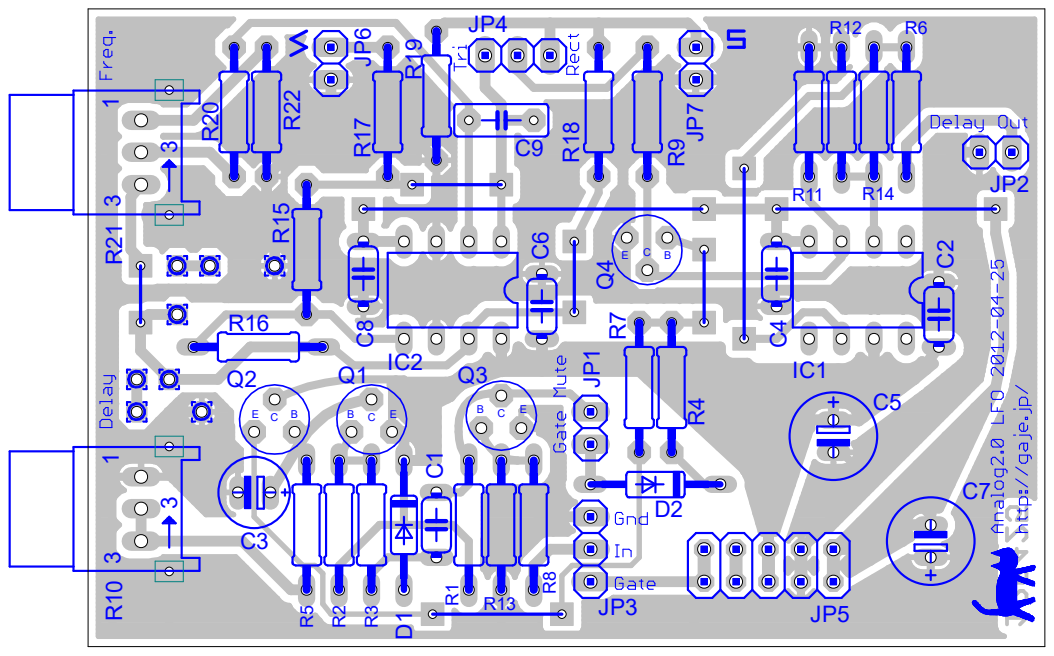
[picture p152: page 1]
