naokiiwakami/analog2.0/08_lfo/lfo_sch.pdf

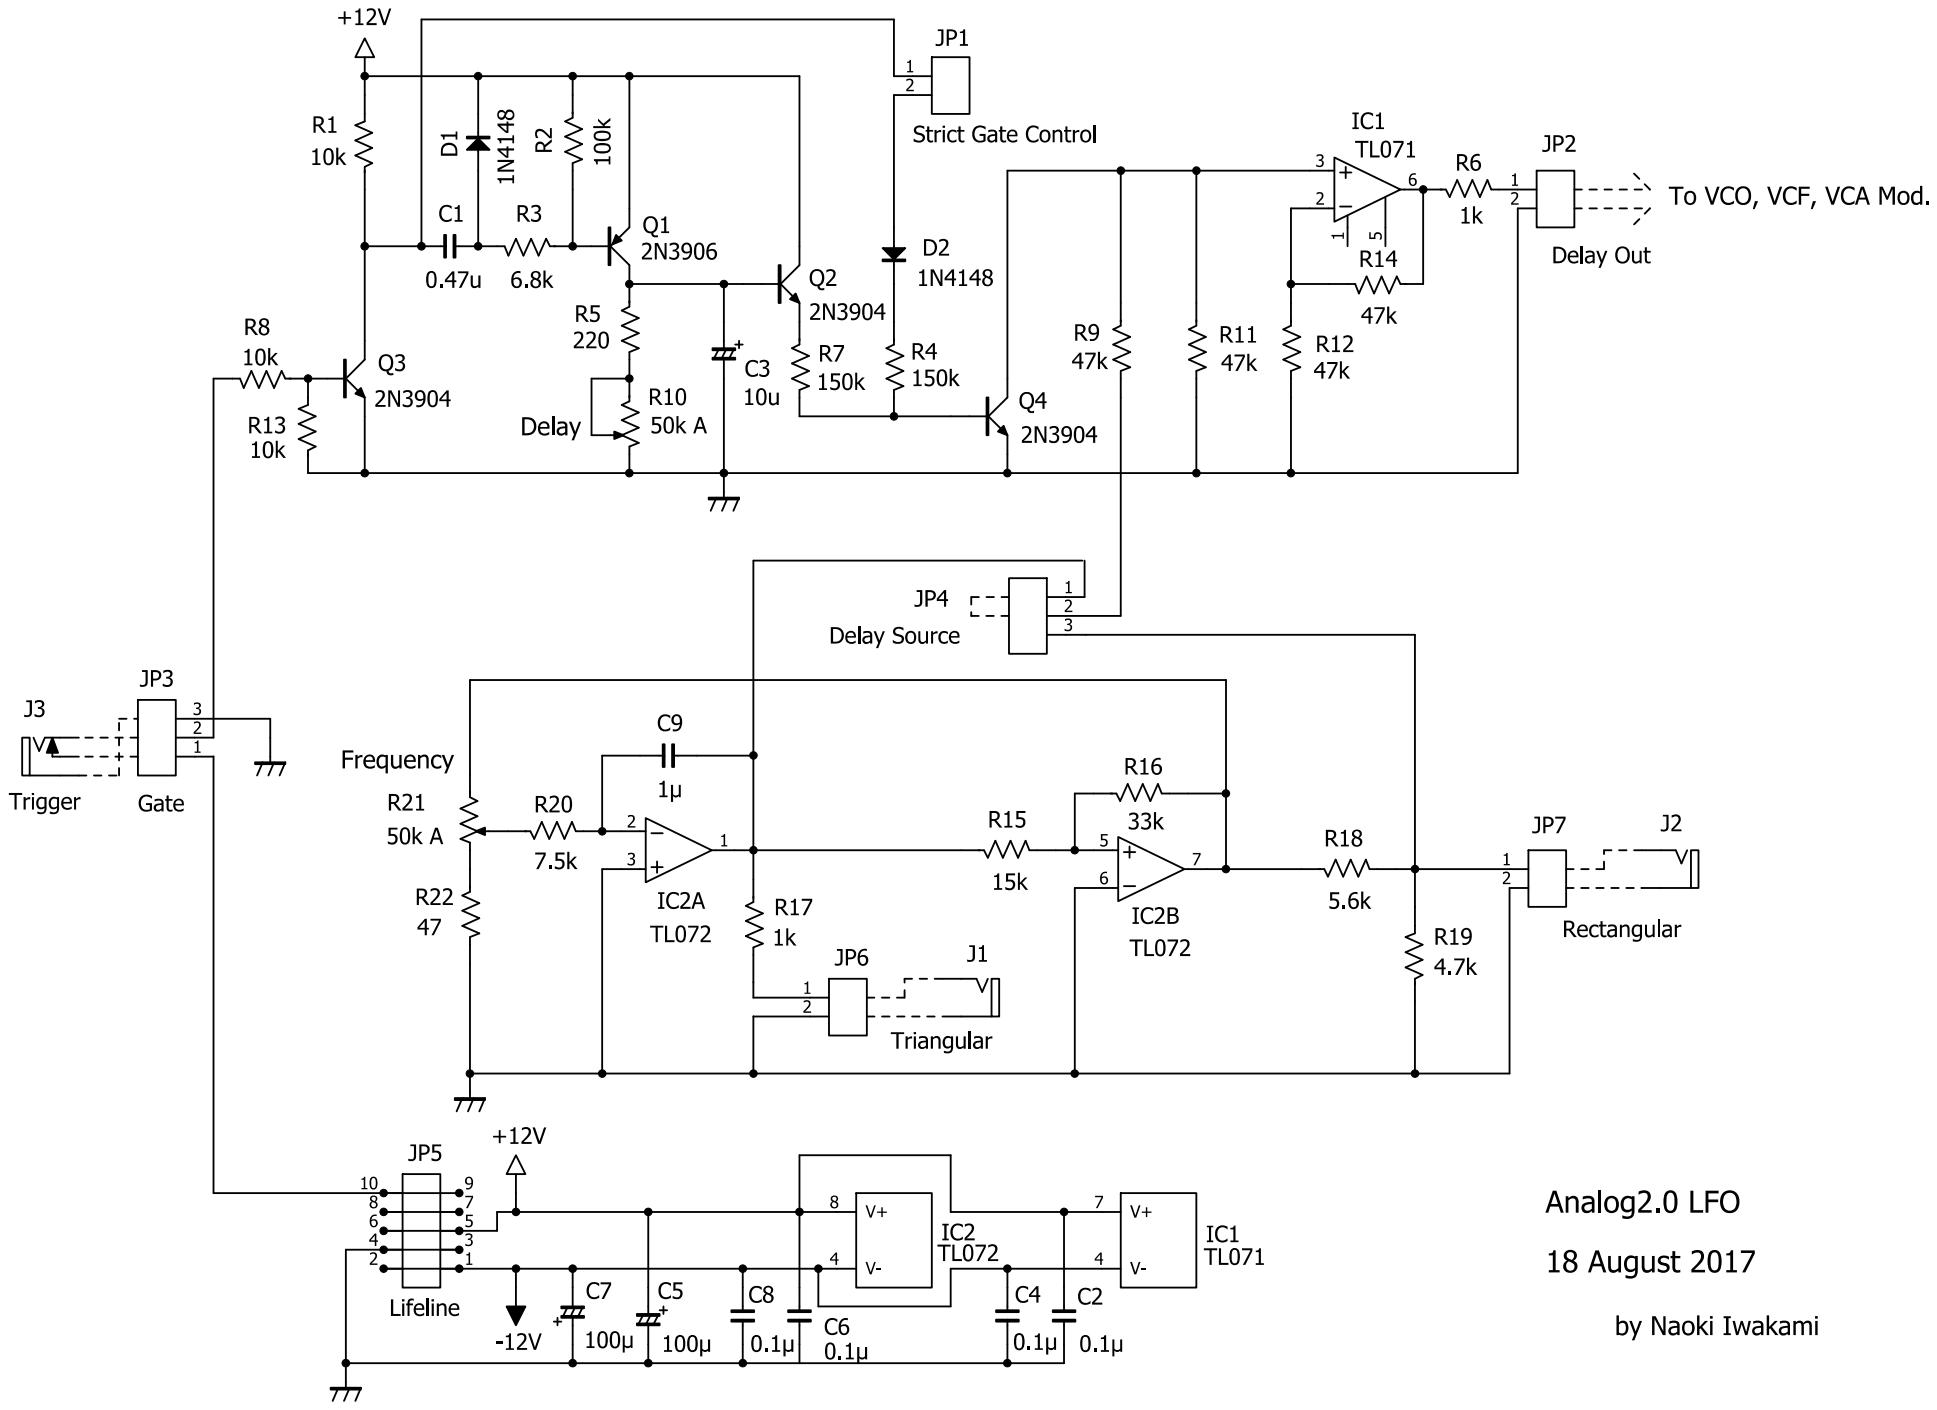
[picture p153: page 1]
