naokiiwakami/analog2.0/09_vcf/vcf_brd.pdf

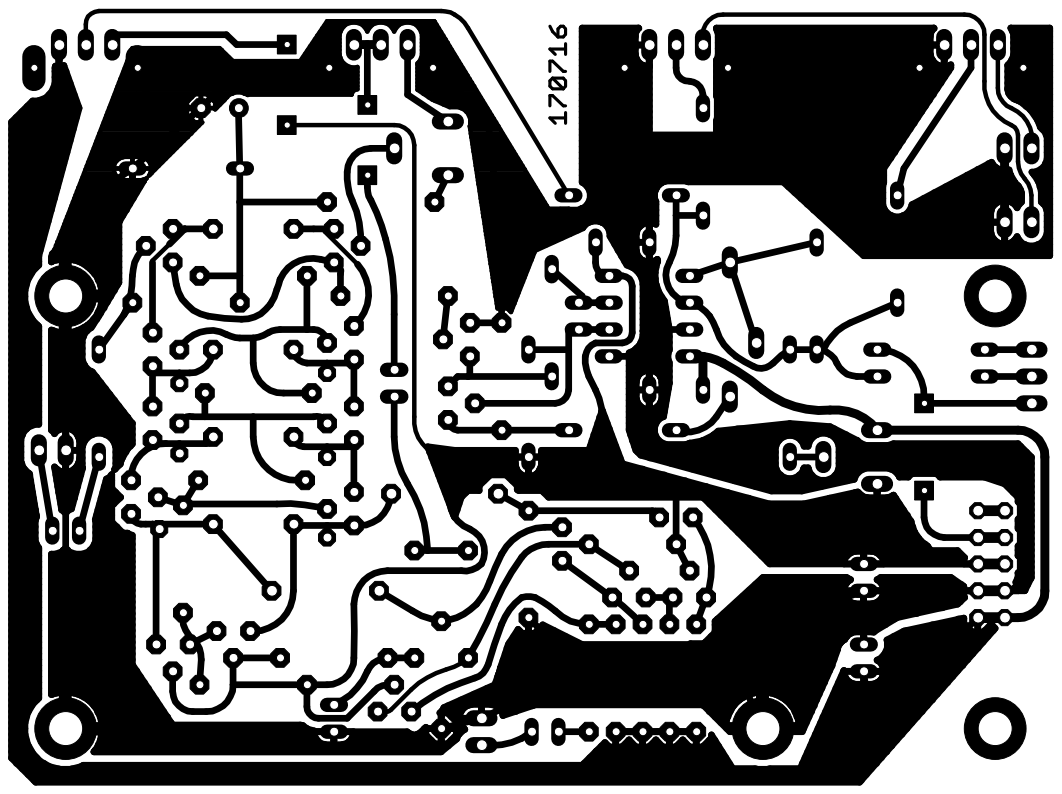
[picture p154: page 1]
