naokiiwakami/analog2.0/09_vcf/vcf_brd_cmp.pdf

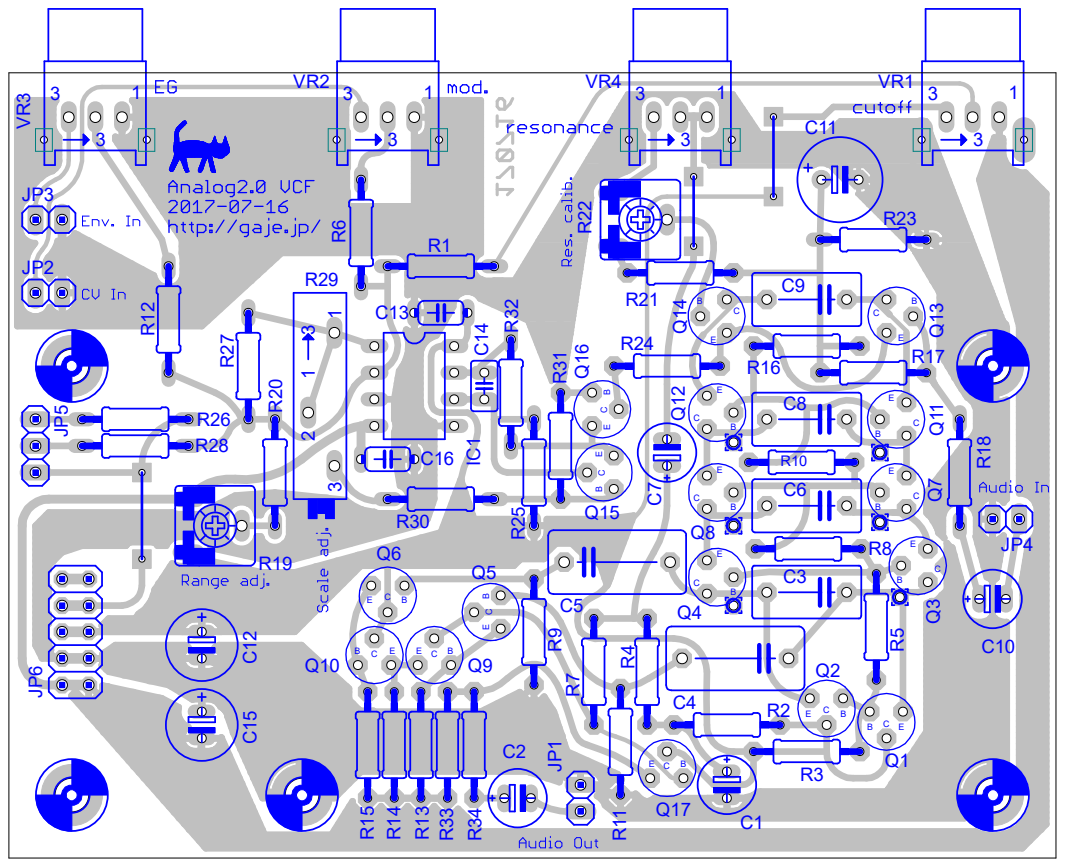
[picture p155: page 1]
