naokiiwakami/analog2.0/09_vcf/vcf_sch.pdf

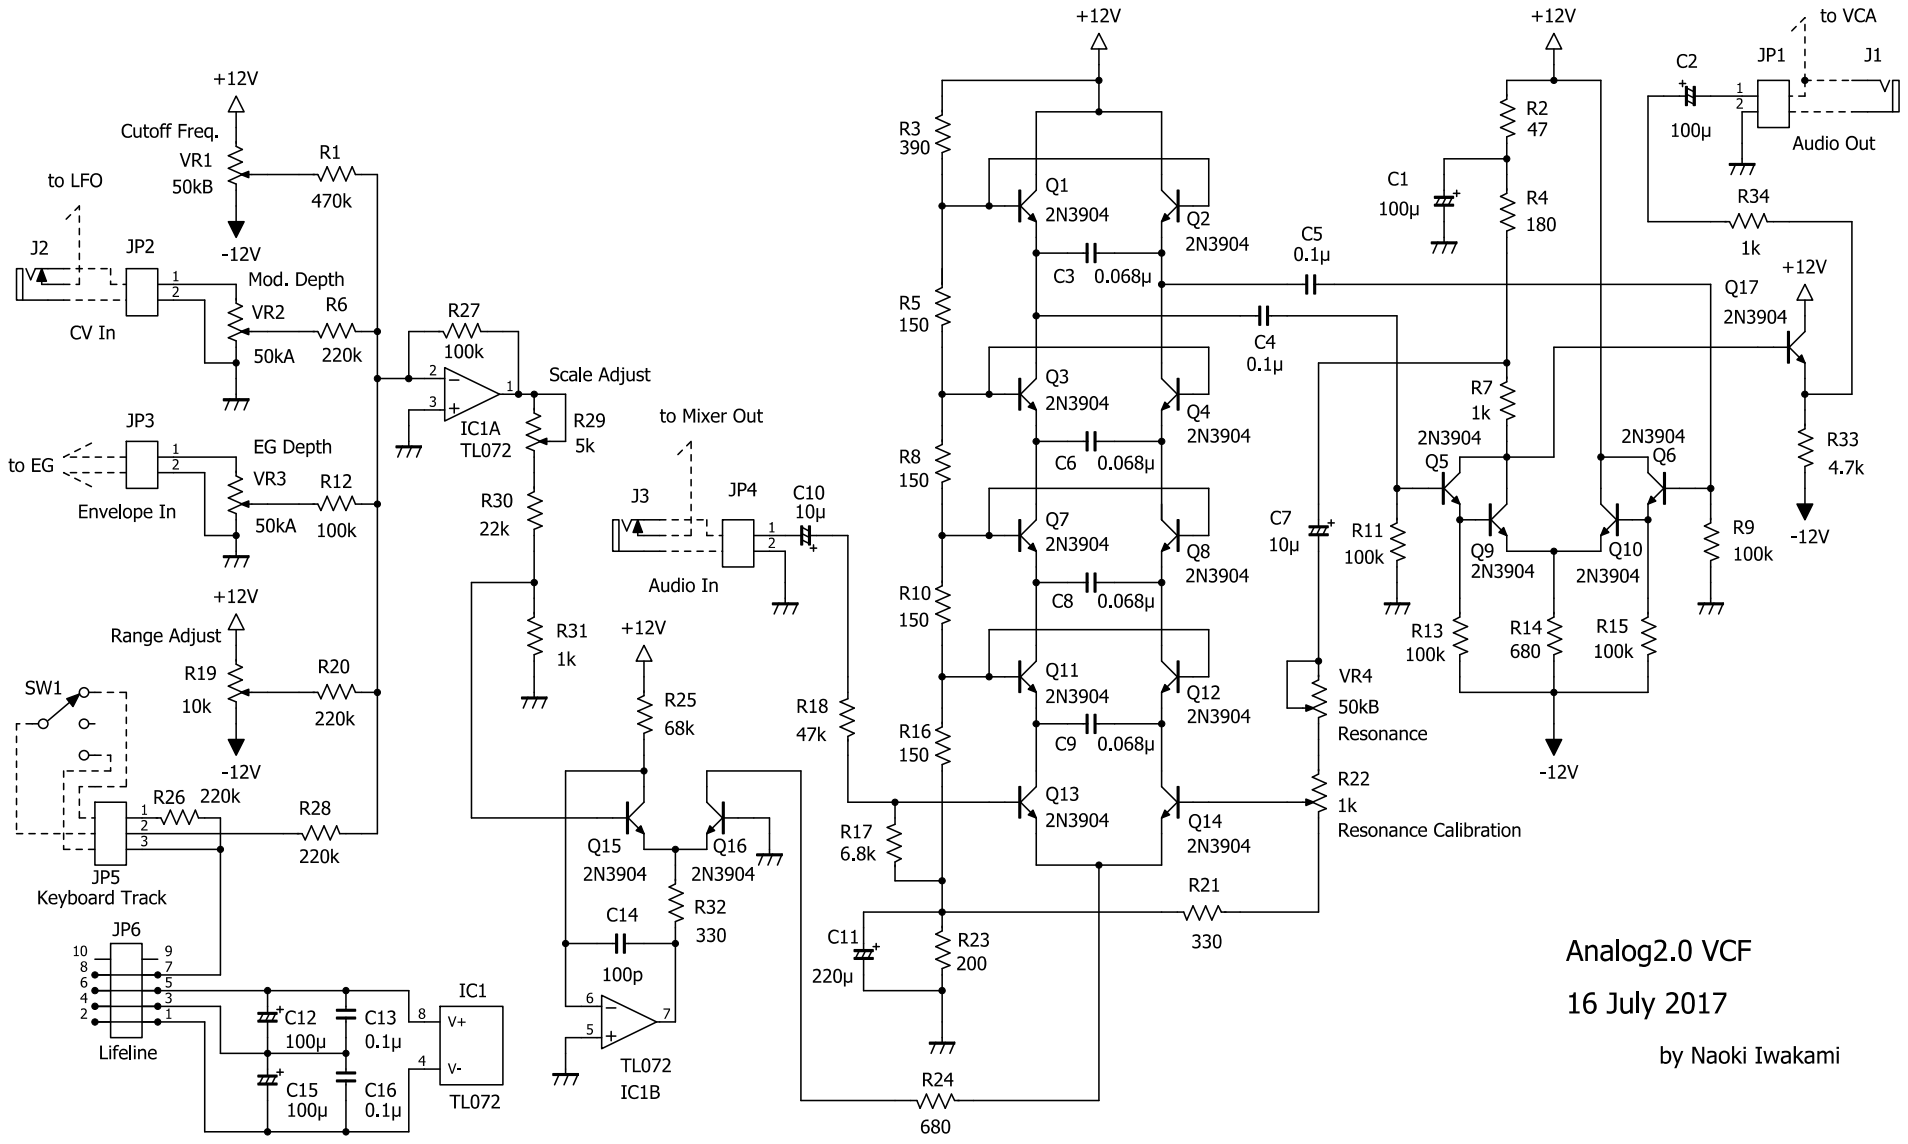
[picture p156: page 1]
