naokiiwakami/analog2.0/10_miniboard/miniboard_brd.pdf

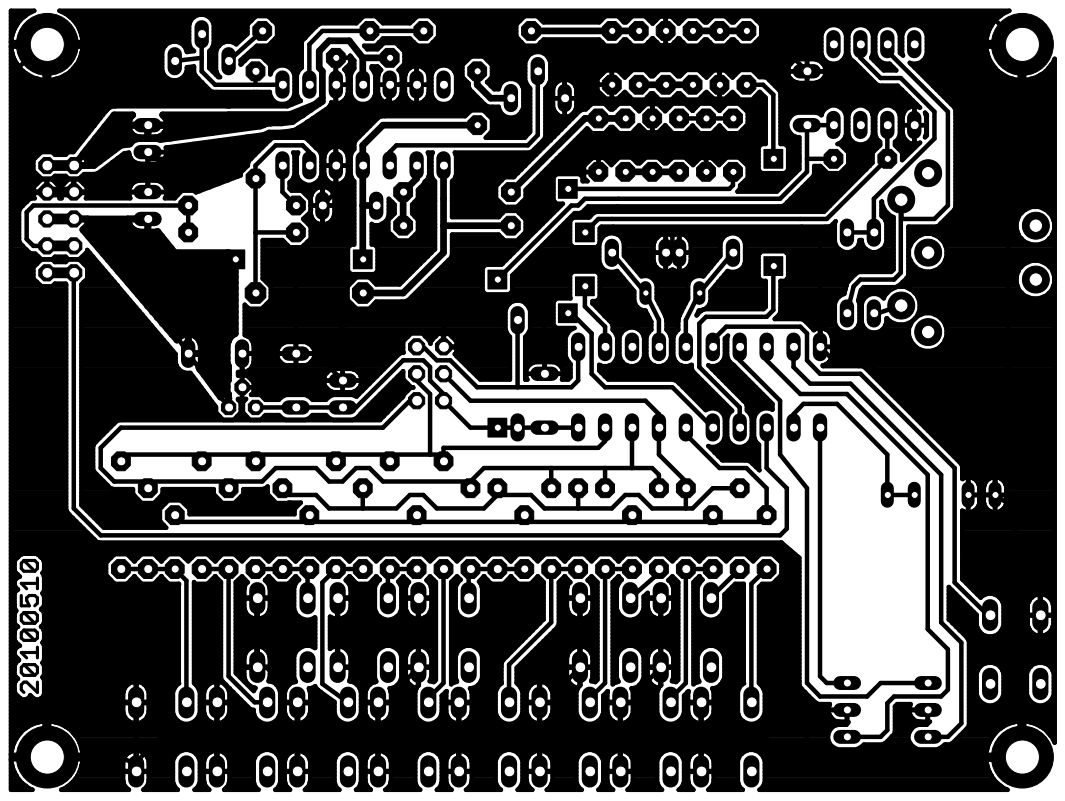
[picture p157: page 1]
