naokiiwakami/analog2.0/04_noise_mixer/noise_mixer_sch.pdf

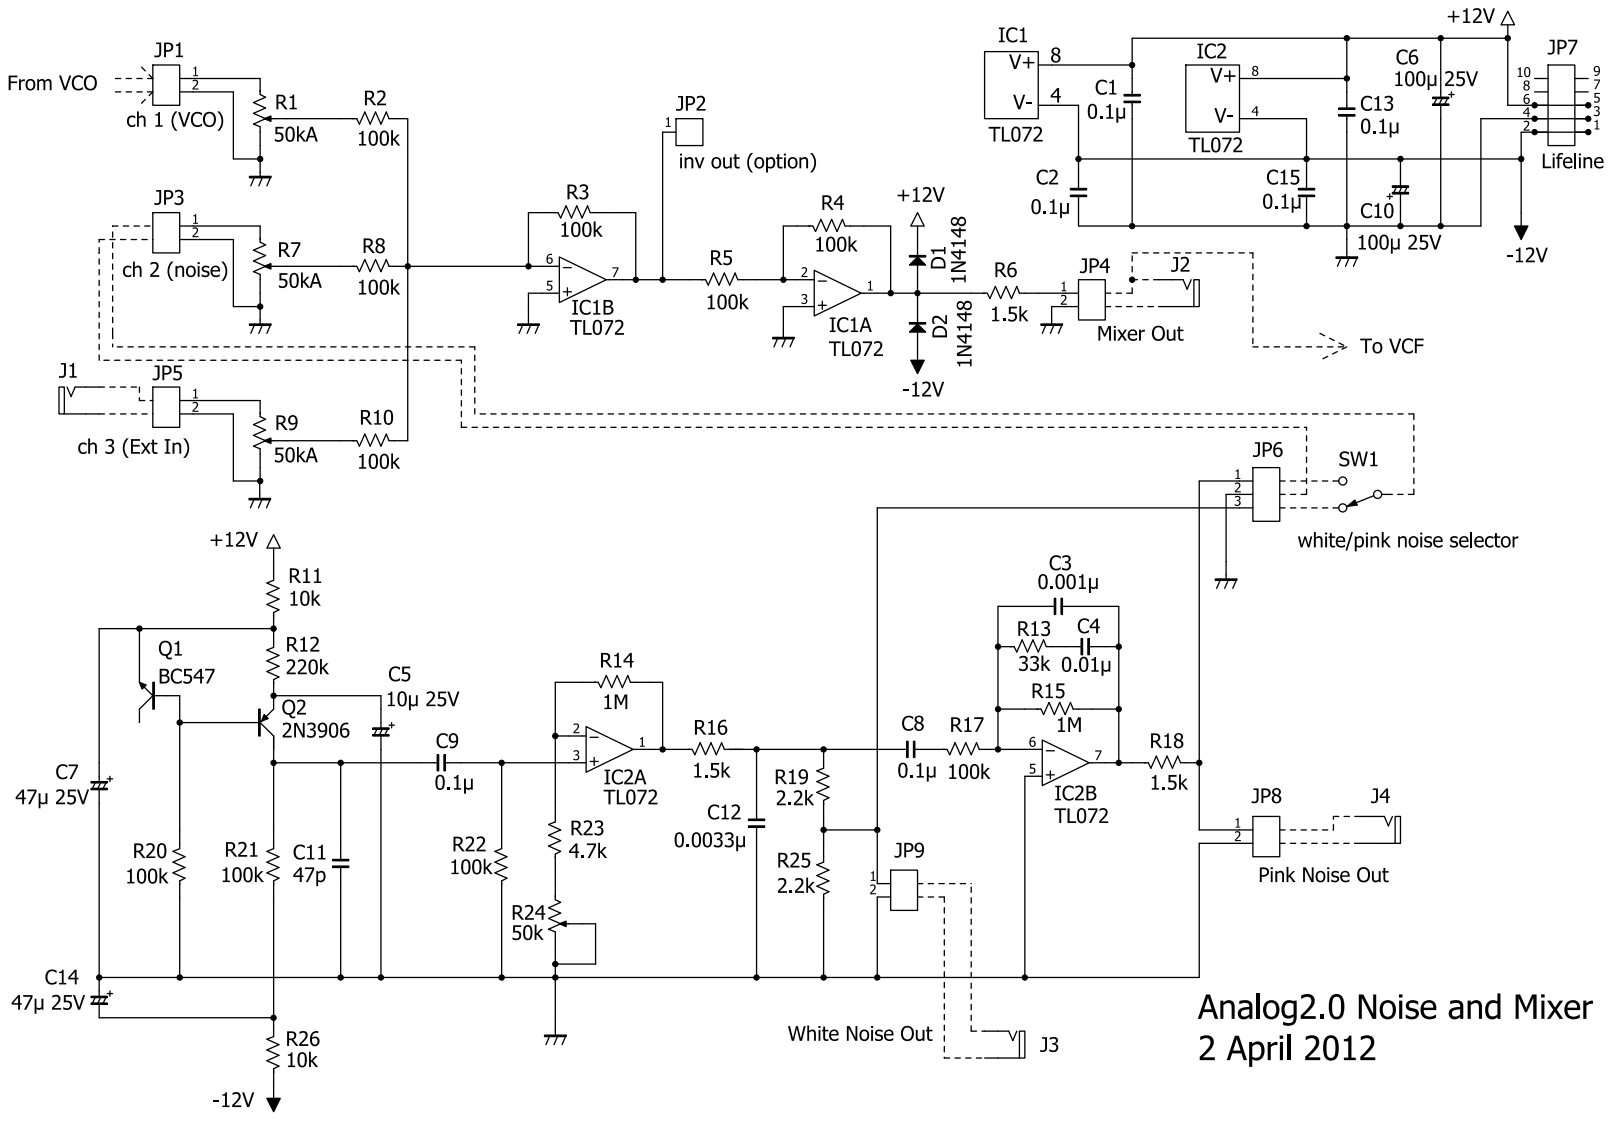
[picture p158: page 1]
