naokiiwakami/analog2.0/04_noise_mixer/noise_mixer_brd.pdf

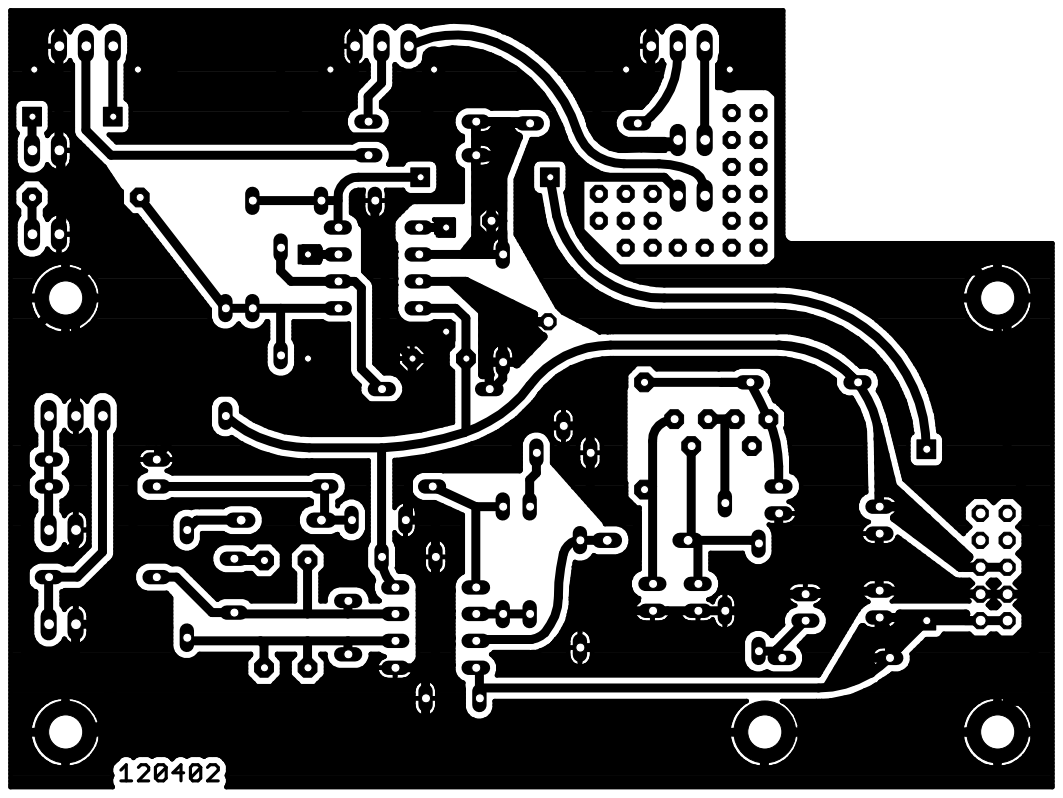
[picture p159: page 1]
