naokiiwakami/analog2.0/04_noise_mixer/noise_mixer_brd_cmp.pdf

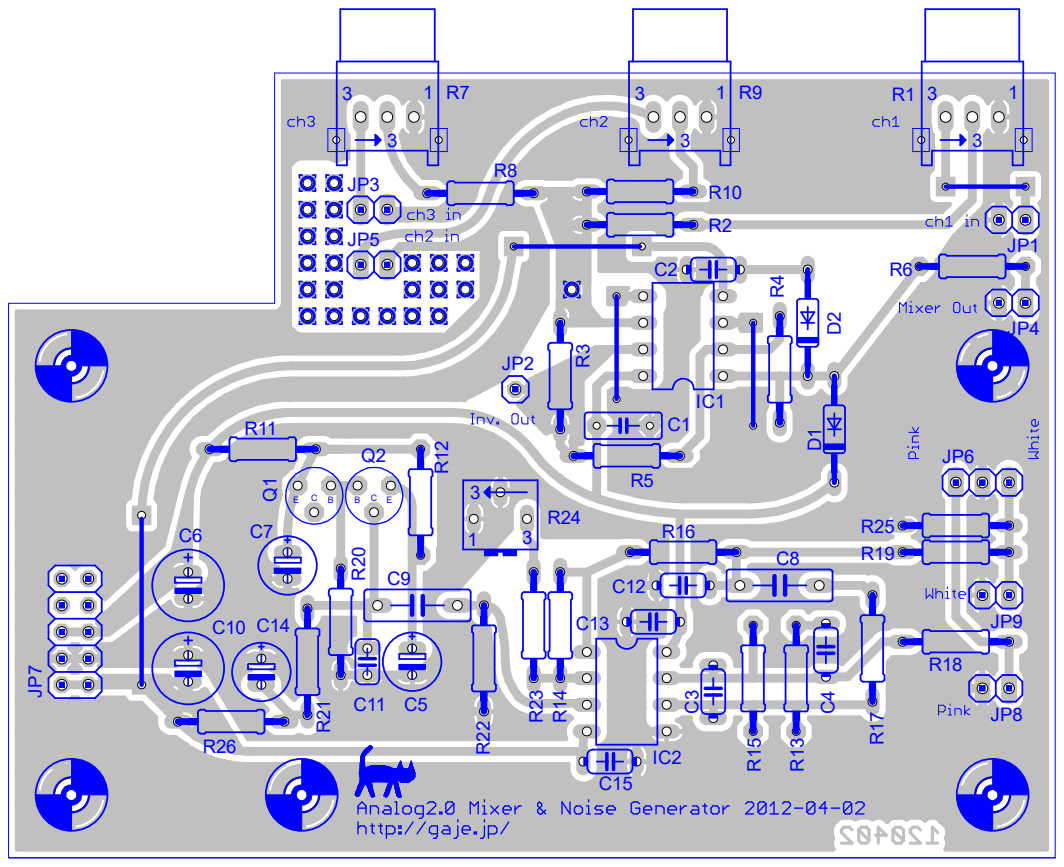
[picture p160: page 1]
