naokiiwakami/analog2.0/02_panel/panel.pdf

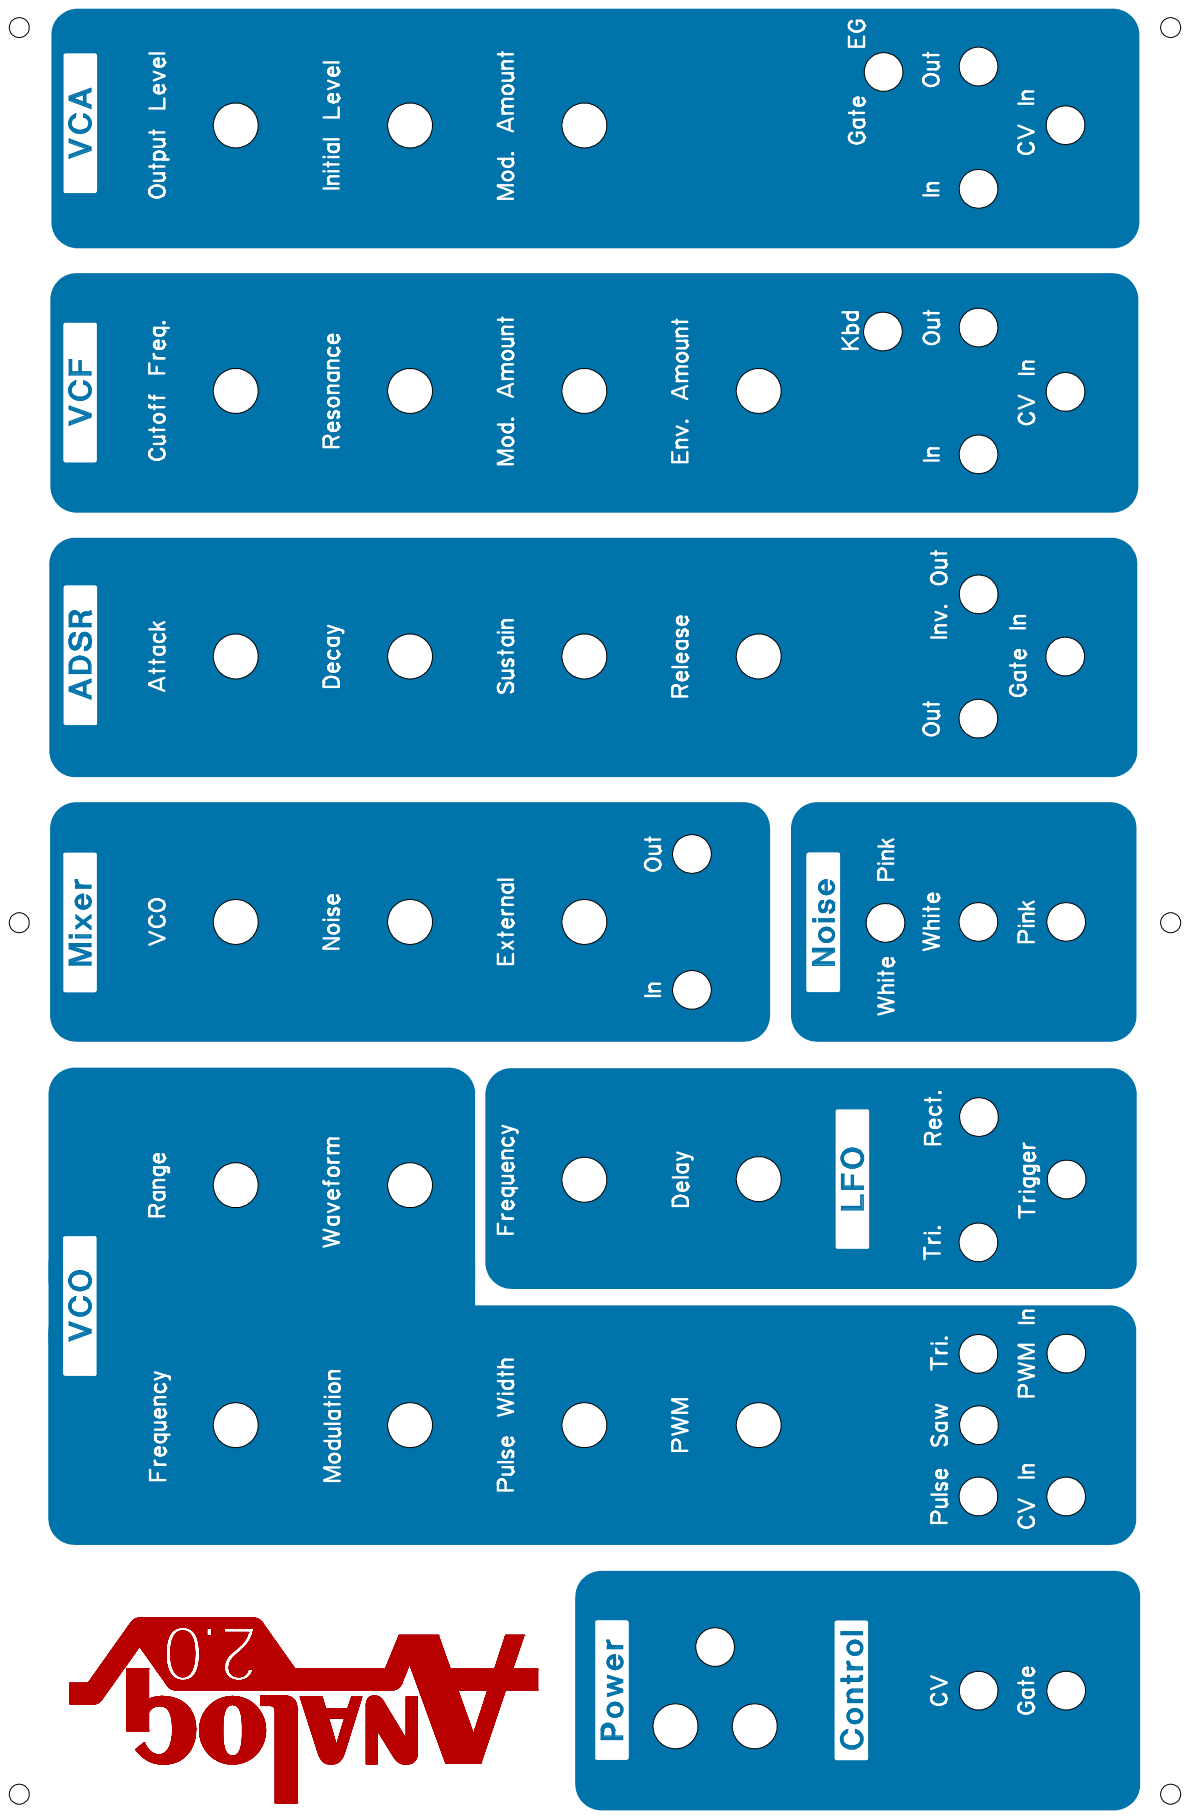
[picture p161: page 1]
