naokiiwakami/analog2.0/02_panel/panel_with_centermarks.pdf

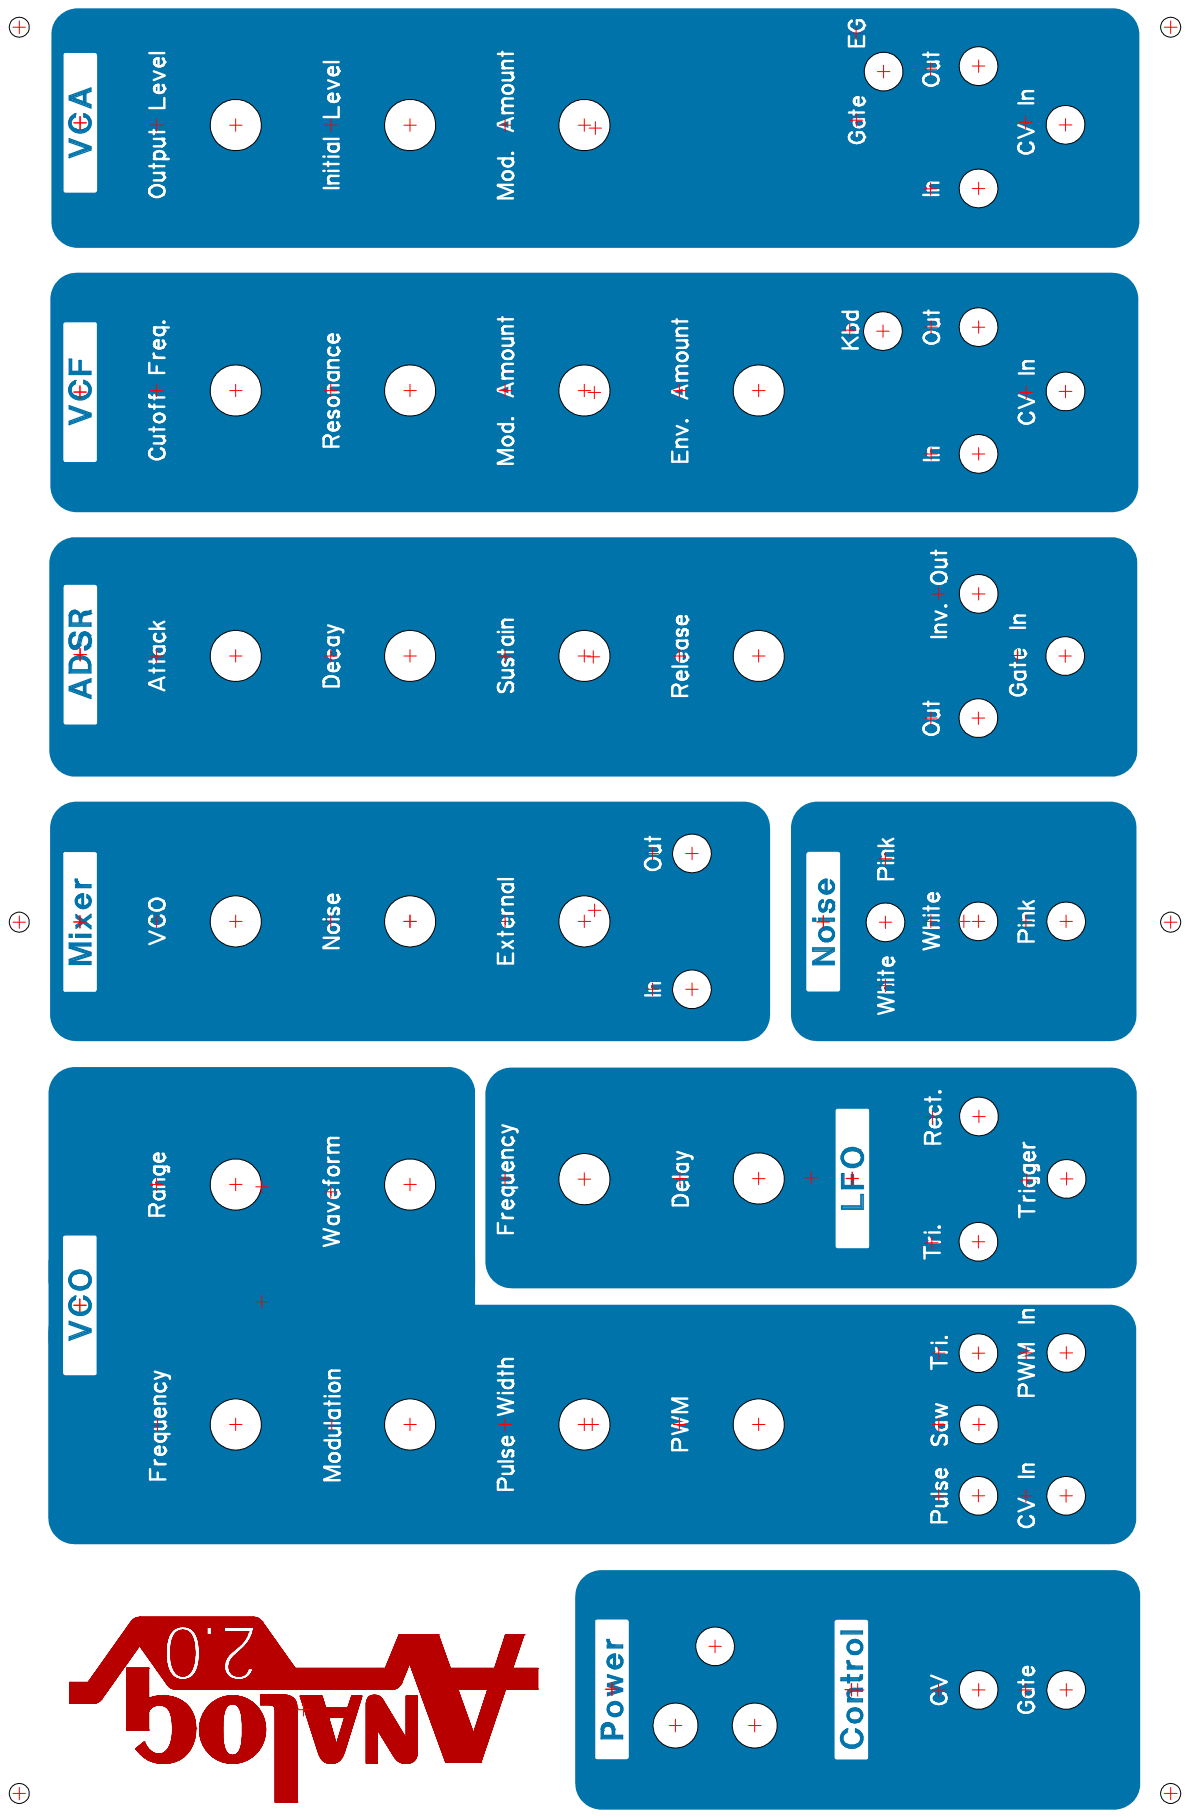
[picture p162: page 1]
