naokiiwakami/analog2.0/03_power/power_brd.pdf

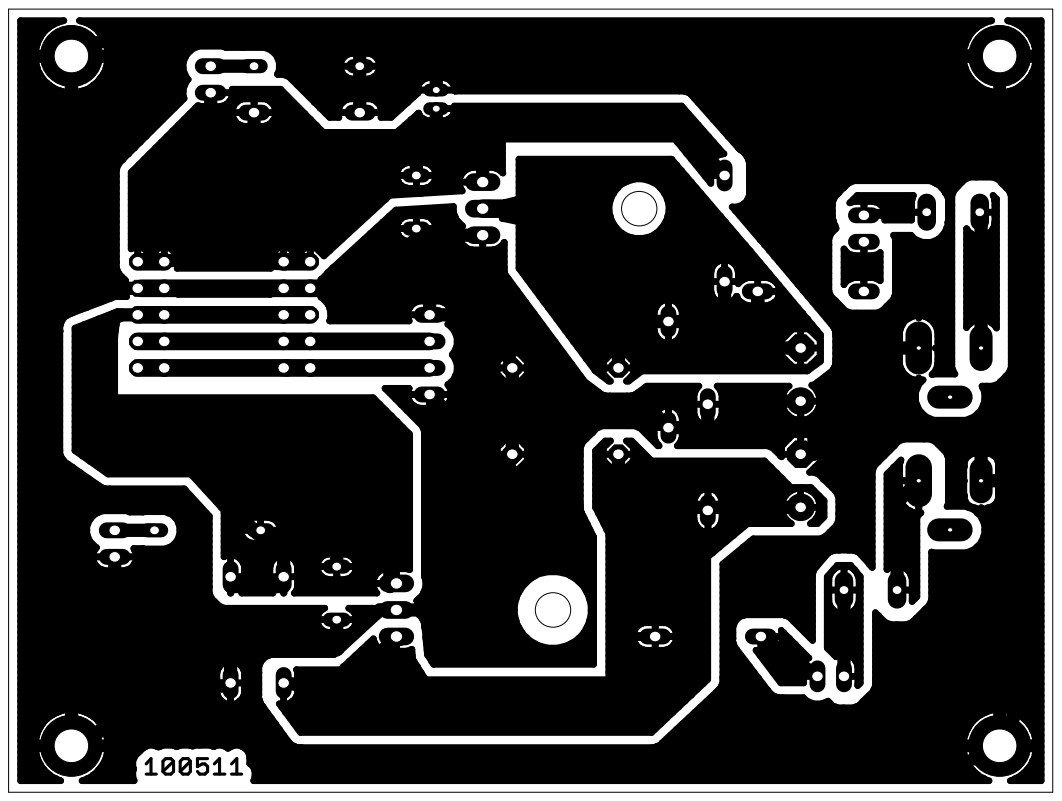
[picture p163: page 1]
