naokiiwakami/analog2.0/03_power/power_brd_cmp.pdf

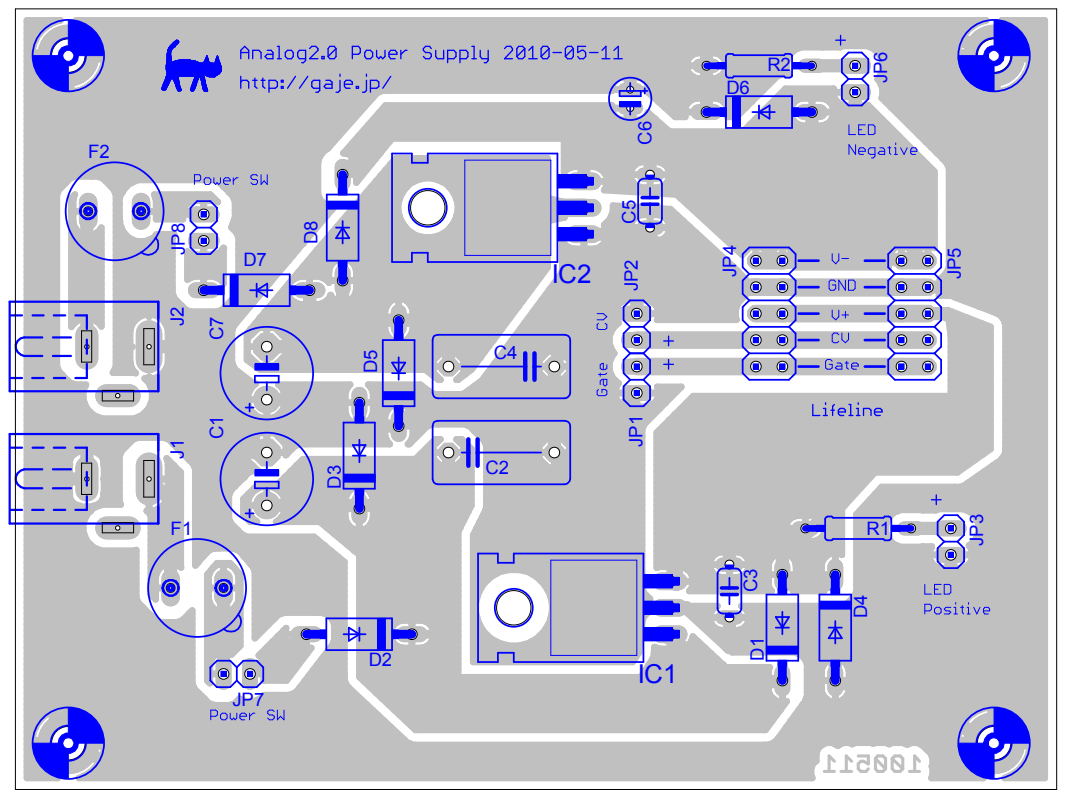
[picture p164: page 1]
