naokiiwakami/analog2.0/10_miniboard/miniboard_brd_cmp.pdf

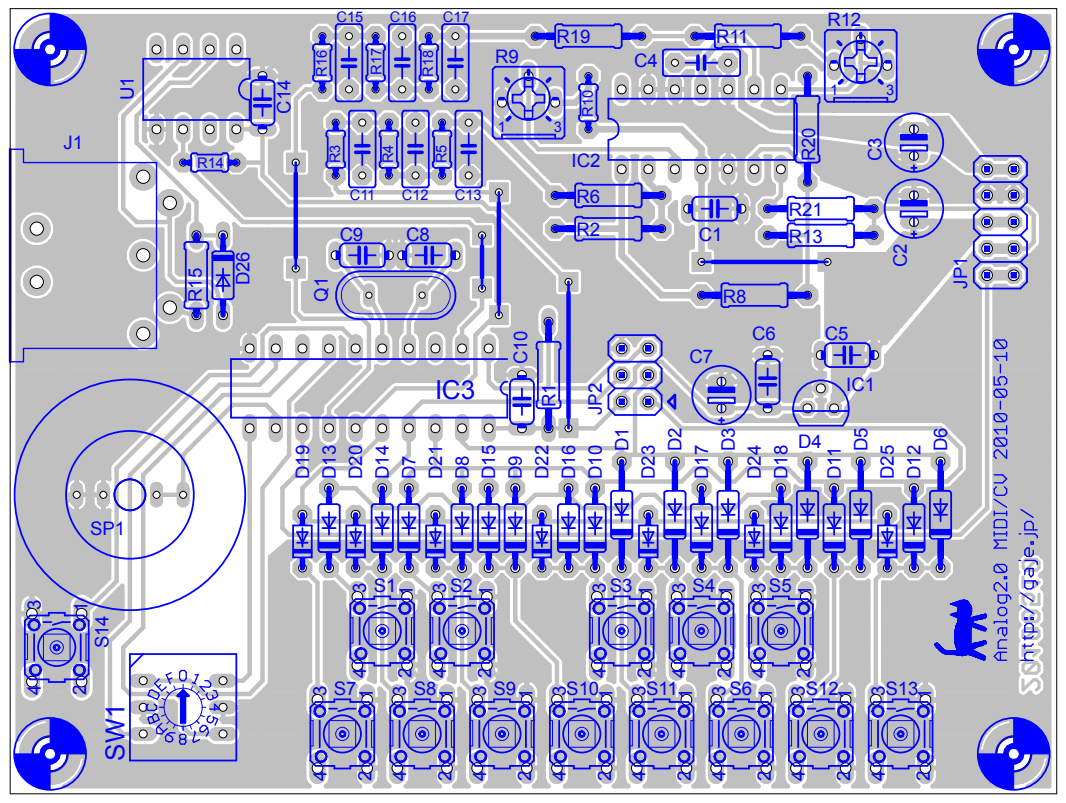
[picture p165: page 1]
