naokiiwakami/analog2.0/others/phase_shifter/phase_shifter_sch.pdf

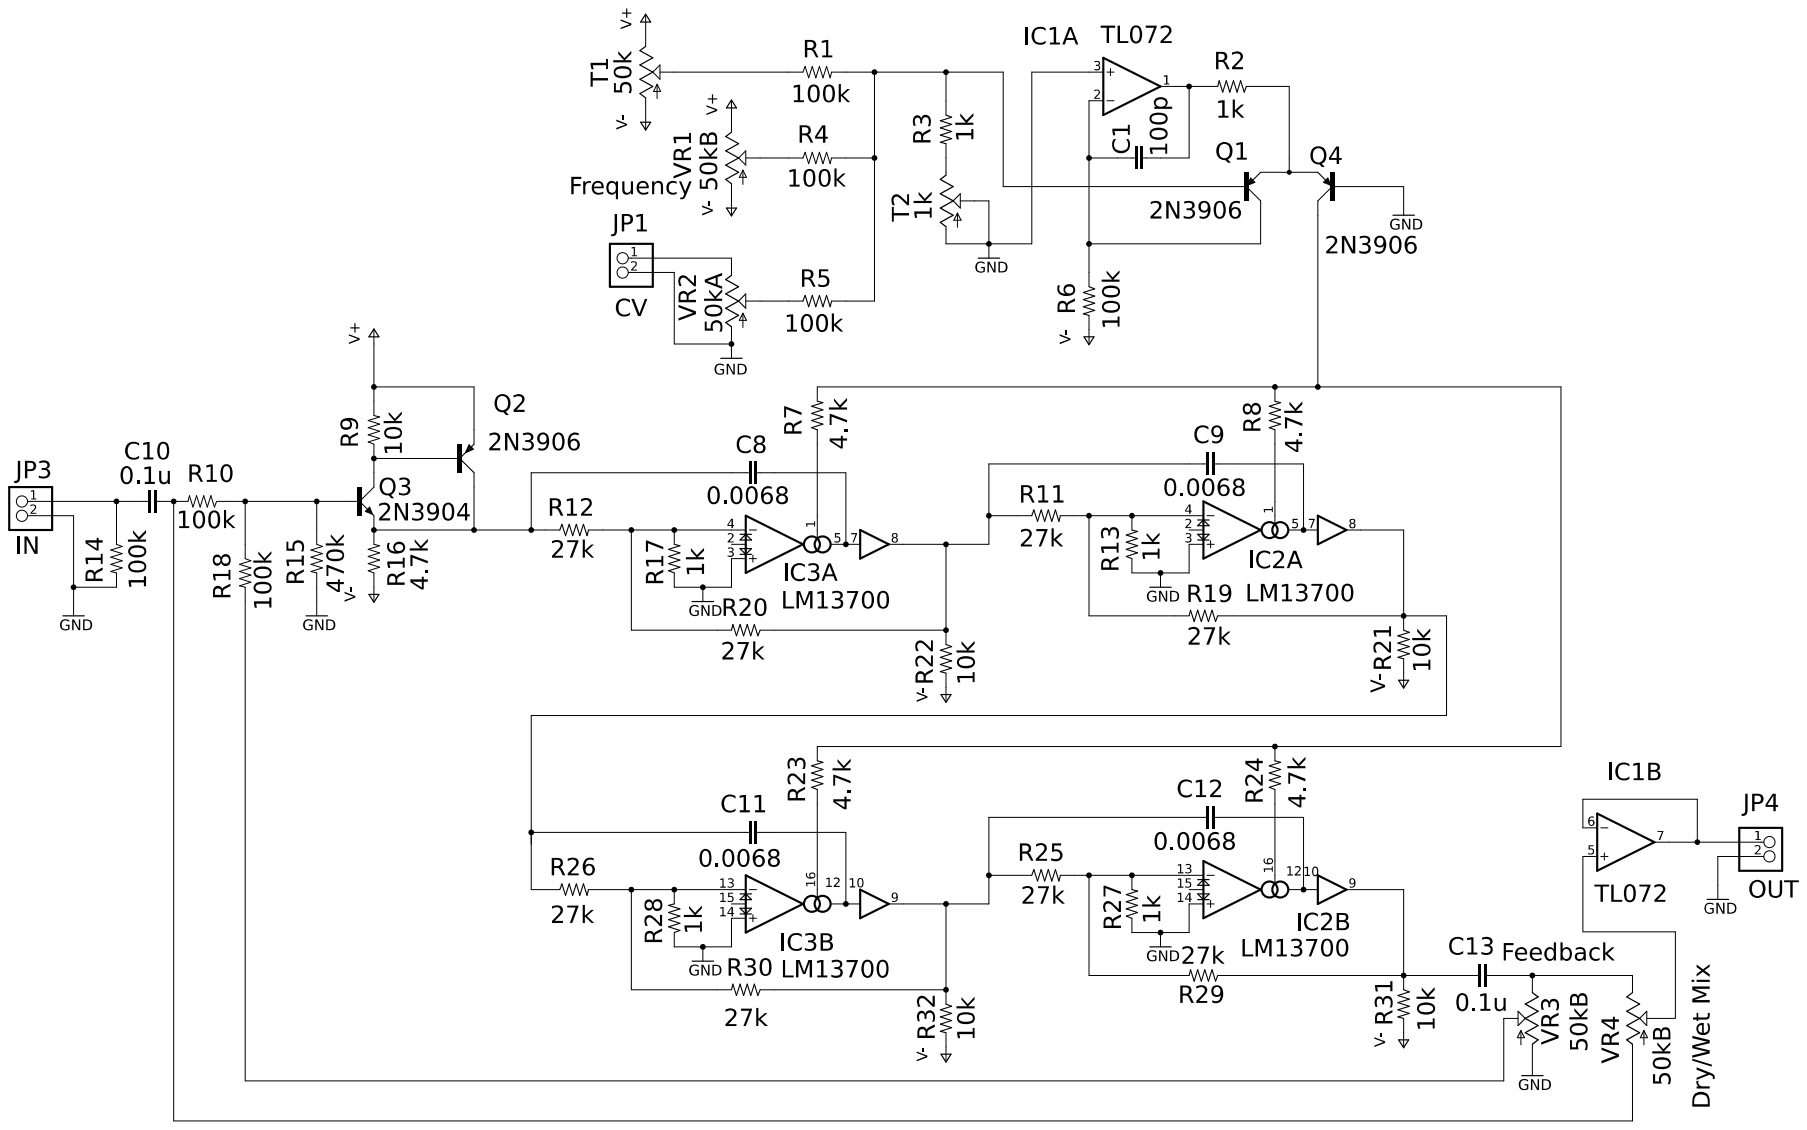
[picture p166: page 1]
