naokiiwakami/analog2.0/others/analog_sequencer/analog_sequencer_sch.pdf

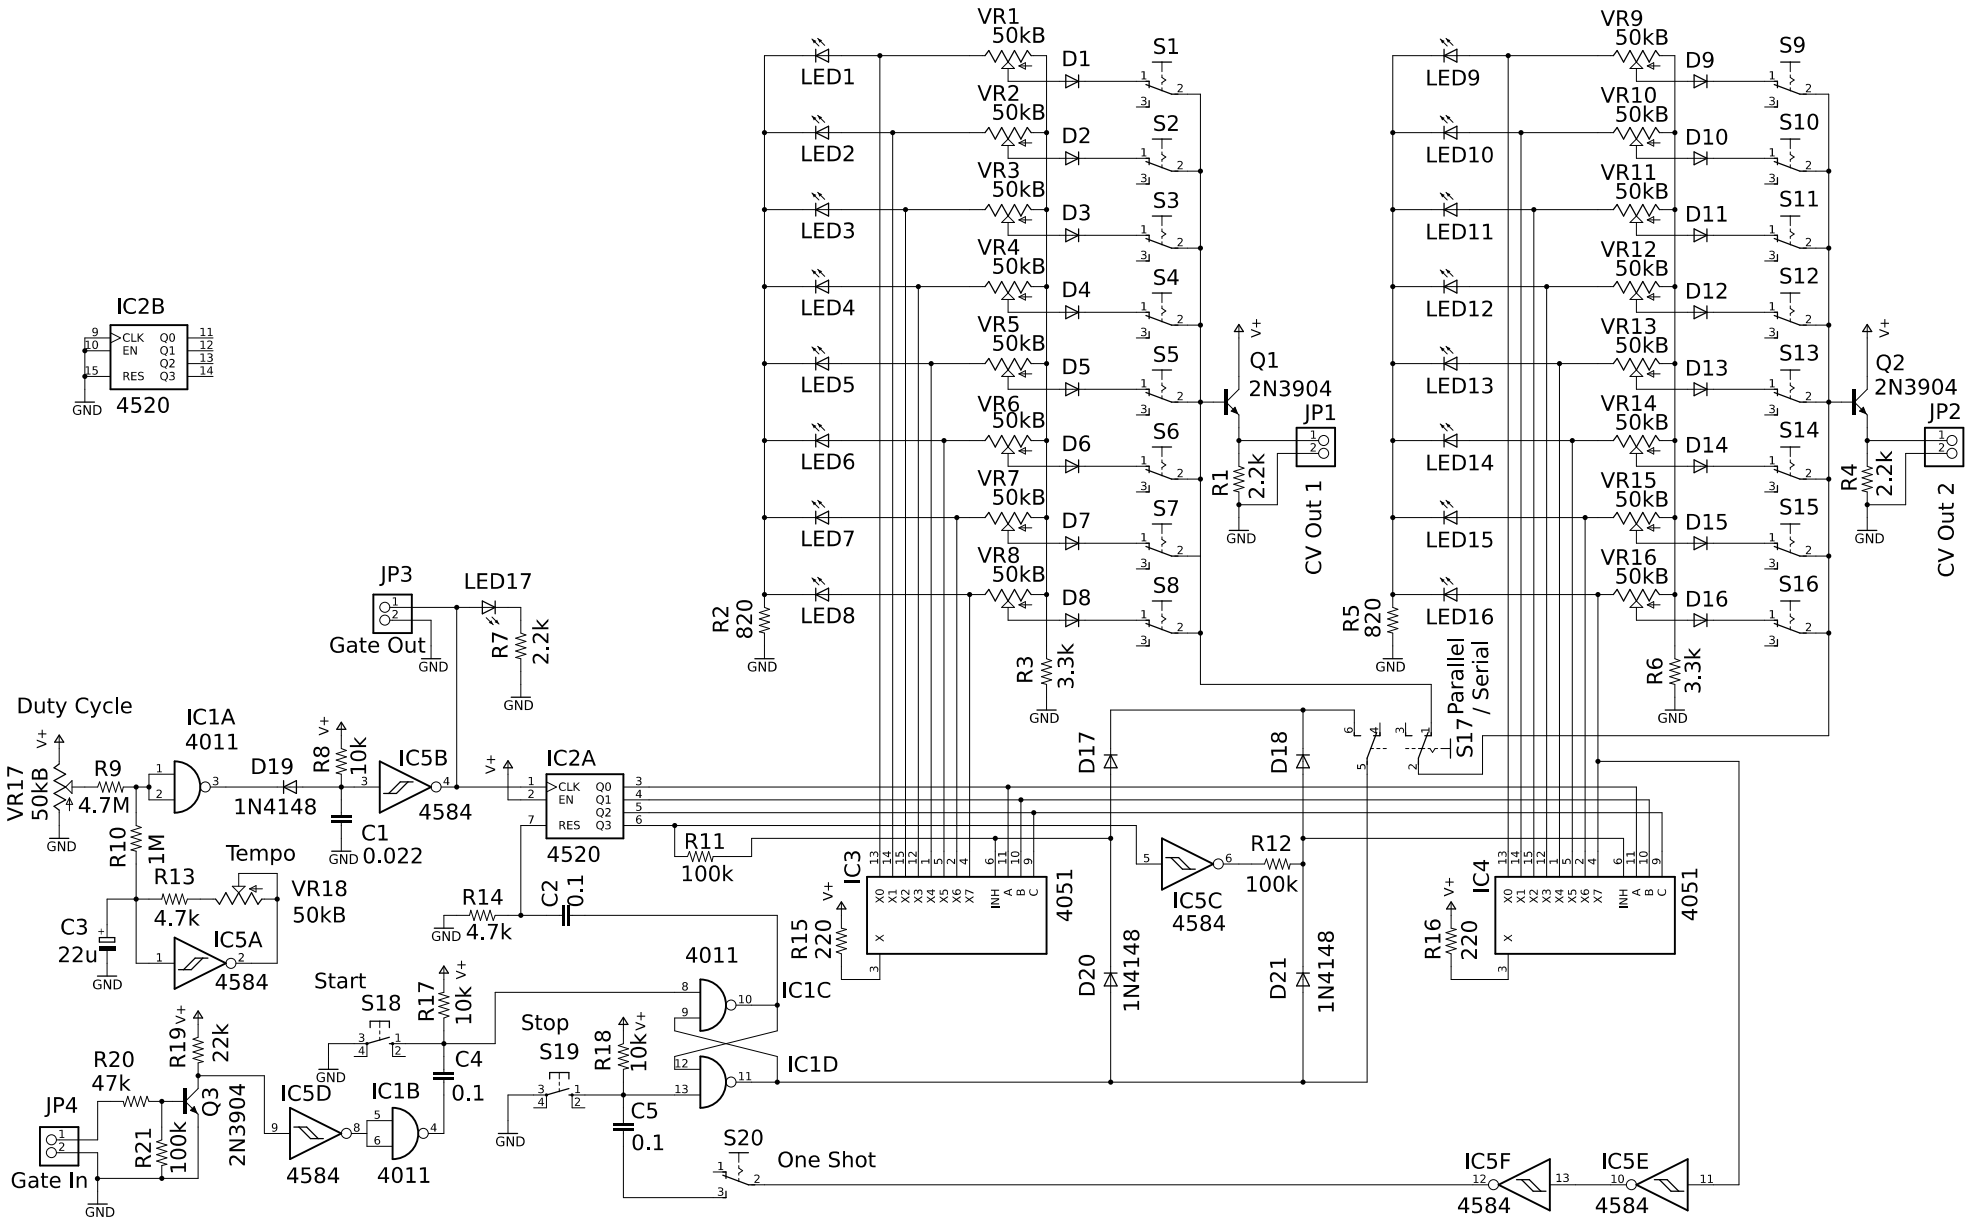
[picture p167: page 1]
