naokiiwakami/analog2.0/others/gate_delay/gate_delay_sch.pdf

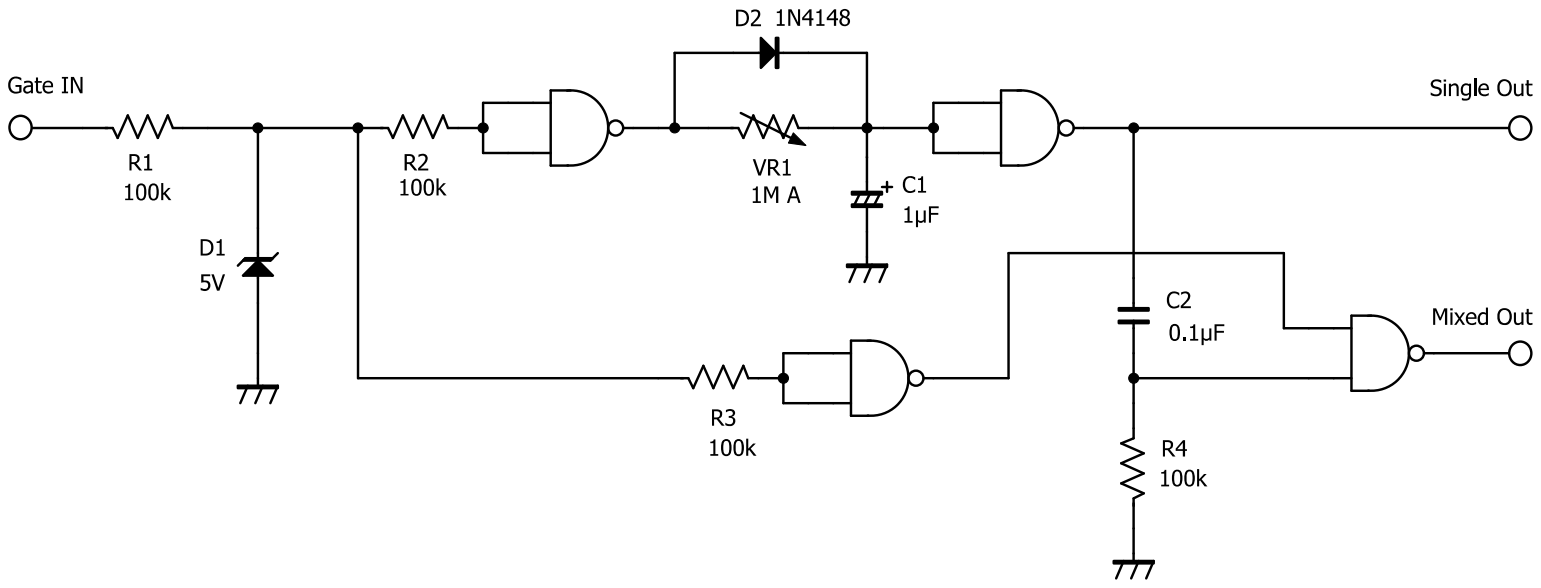
[picture p168: page 1]
