naokiiwakami/analog2.0/others/graphic_equalizer/graphic_equalizer_sch.pdf

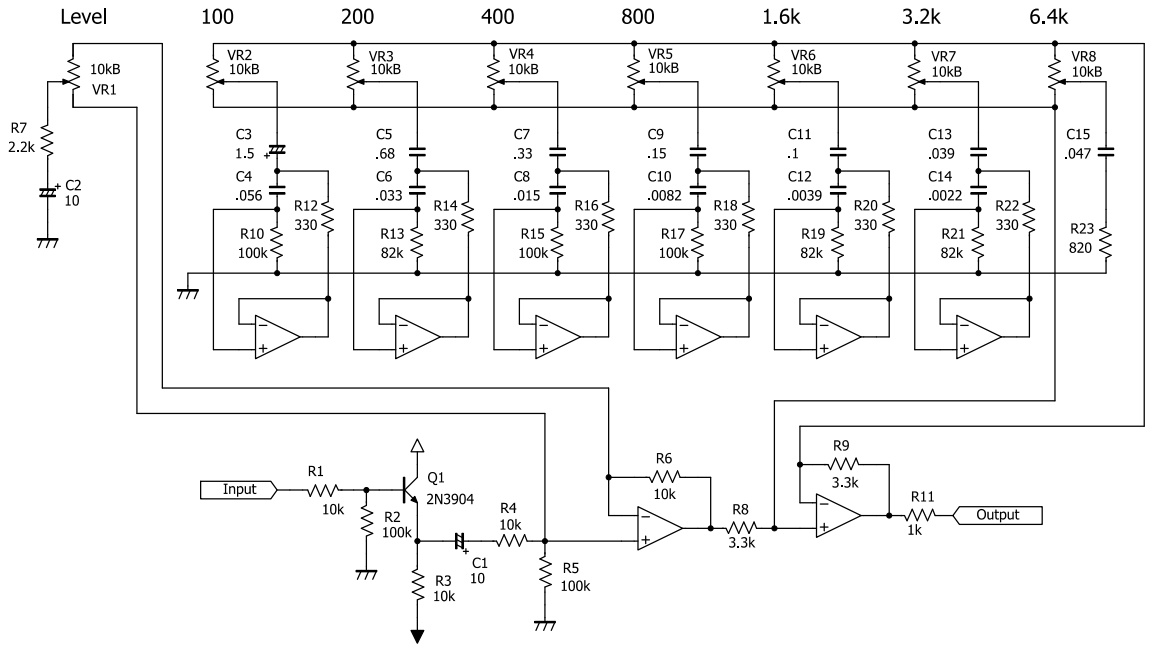
[picture p169: page 1]
