naokiiwakami/analog2.0/others/resonator/resonator_sch.pdf

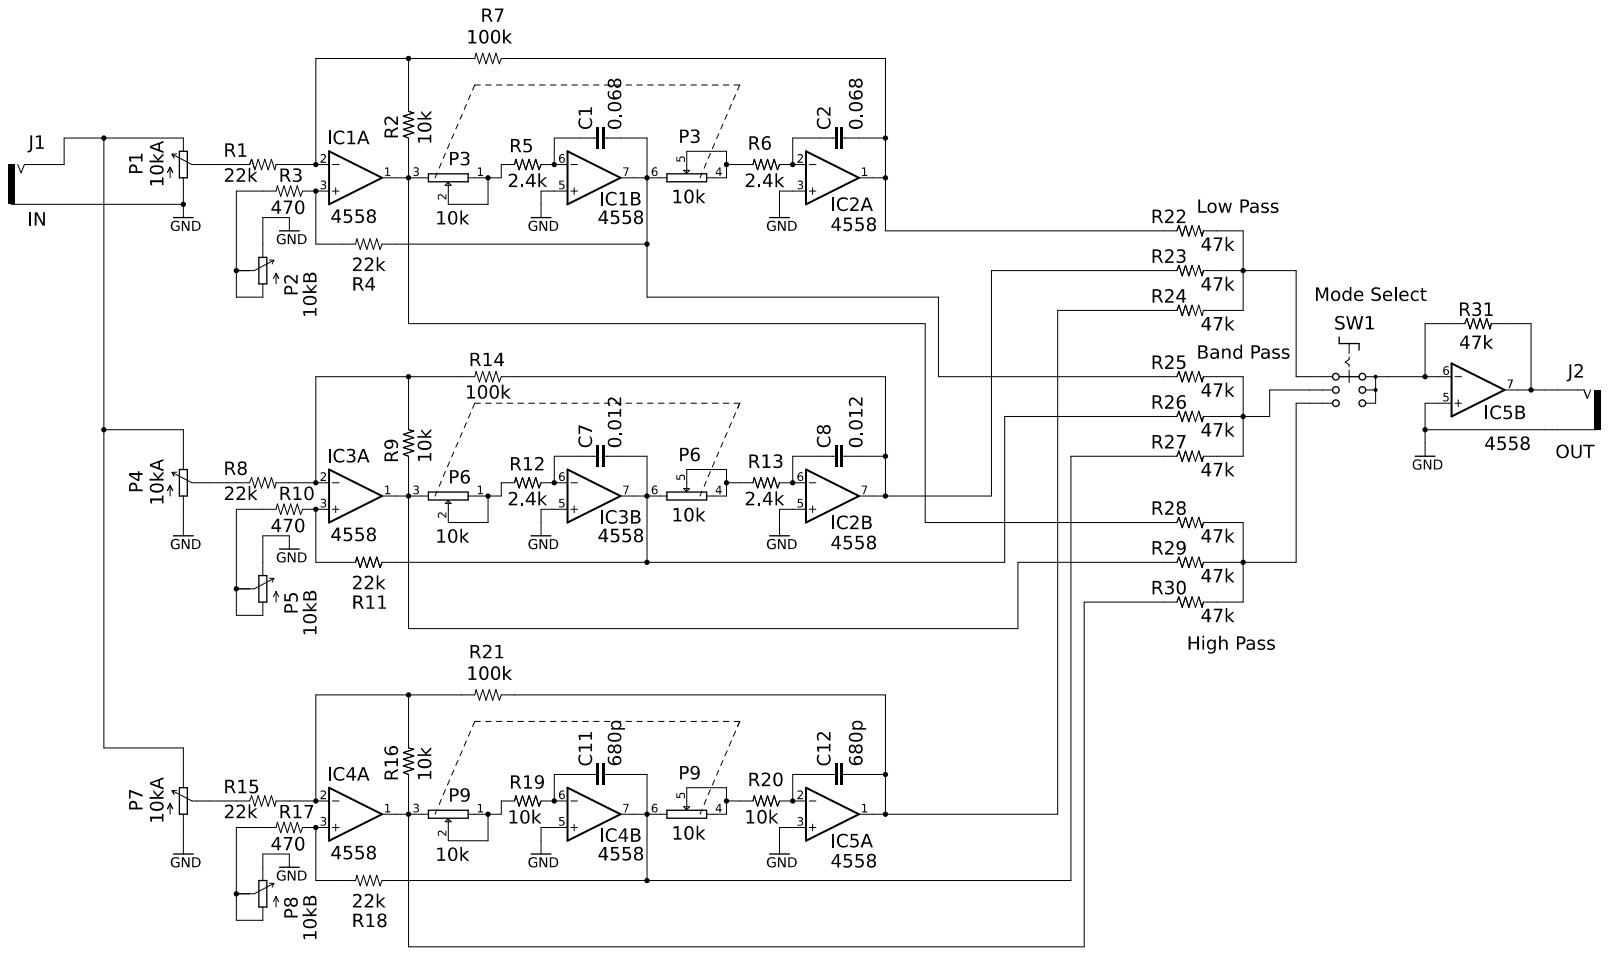
[picture p170: page 1]
