naokiiwakami/analog2.0/others/ring_modulator/ring_modulator_sch.pdf

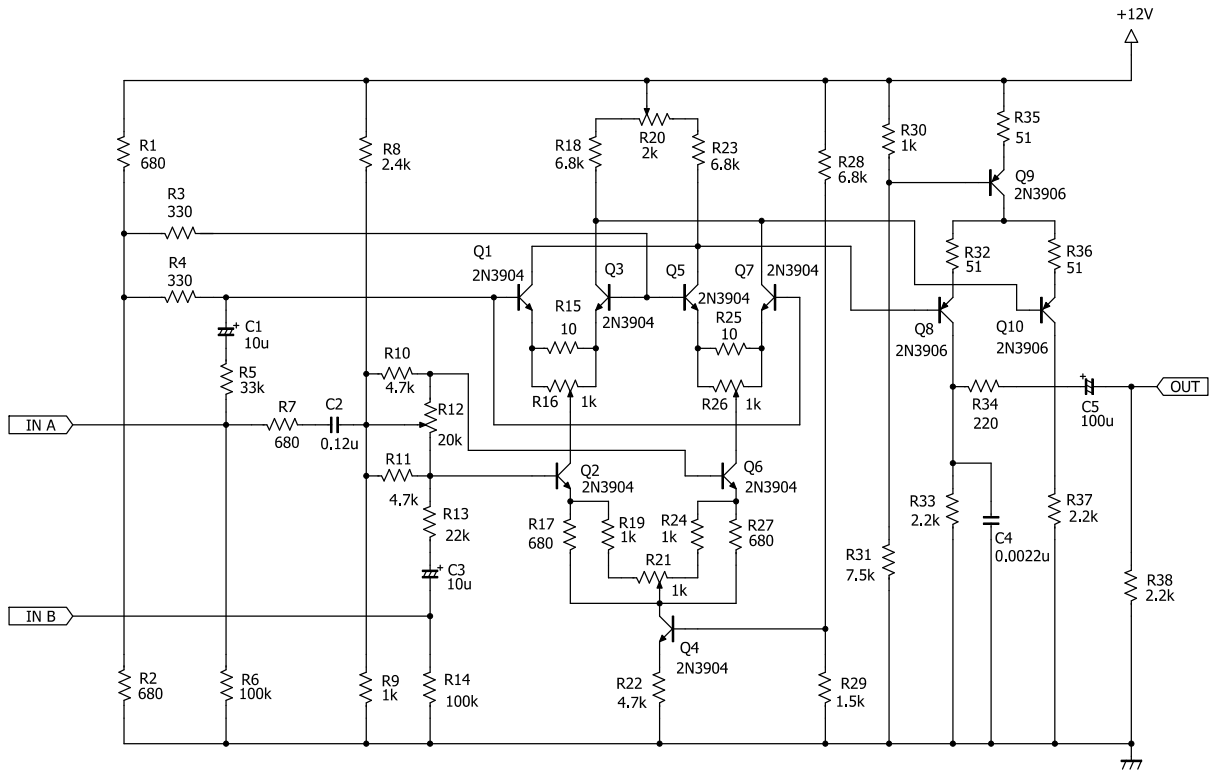
[picture p171: page 1]
